saunair/Stepping-Stones/Mechanical/CAD/Model-F/ss_mf_v1_FR_Top_Plate_Assembly.SLDASM

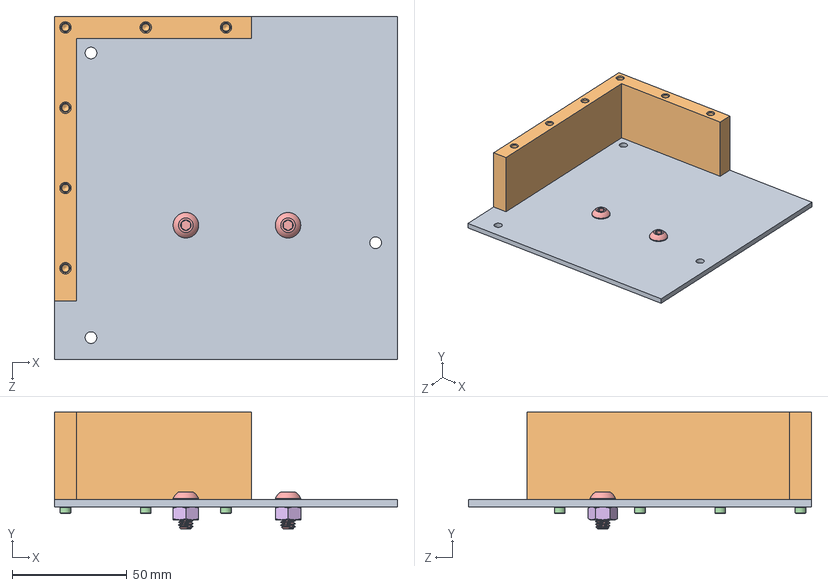
[picture p16: CAD file, 2016-11-26]
Mechanical/CAD/Model-F/ss_mf_v1_FR_Top_Plate_Assembly.SLDASM
149.2 x 50.8 x 149.2 mm
ss_mf_v1_TopPlate
ss_mf_v1_GuideRail
ss_mf_v0_ThreadedInsert440 x 6
ss_mf_v0_Screw_4-40x0.375 x 6
ss_mf_v0_Screw_1_4-20x0.5 x 2
ss_mf_v0_HexNut_1_4-20 x 2
