saunair/Stepping-Stones/Mechanical/CAD/Model-F/Drive Train/ss_mf_v1_DriveTrainAssembly.SLDASM

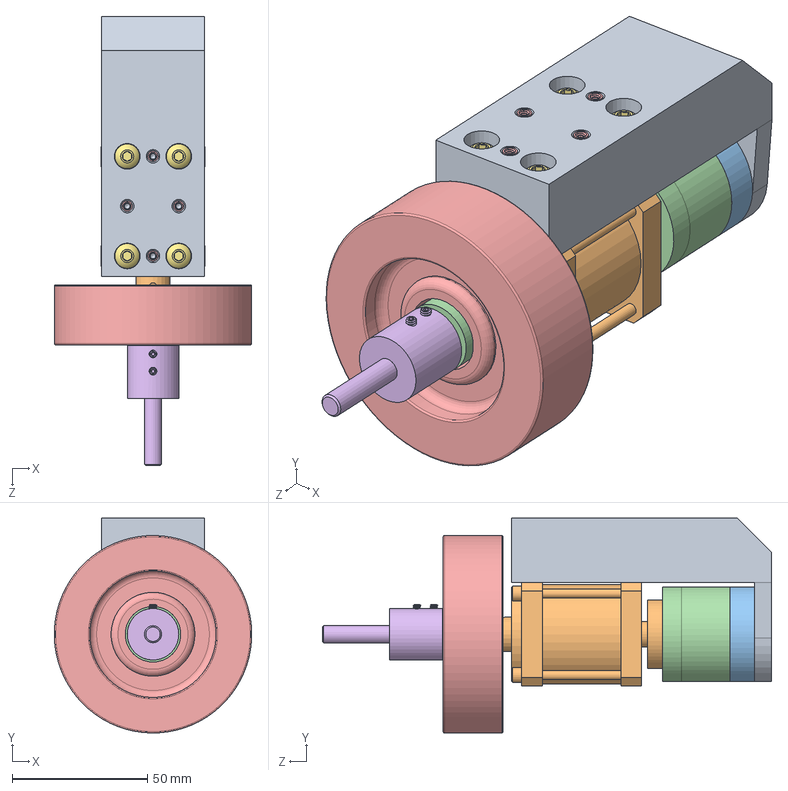
[picture p17: CAD file, 2016-11-26]
Mechanical/CAD/Model-F/Drive Train/ss_mf_v1_DriveTrainAssembly.SLDASM
73.0 x 79.5 x 166.1 mm
ss_mf_v1_GearboxMount
ss_mf_v1_MotorGearboxAdapter
ss_mf_v0_MotorBack
ss_mf_v0_MotorFront
ss_mf_v0_ThreadedInsert440 x 4
ss_mf_v0_SetScrew440 x 2
ss_mf_v0_Screw_10-32x1 x 4
ss_mf_v0_Screw_M3x10 x 4
ss_mf_v0_Screw_M2_5x6 x 3
ss_mf_v0_Gearbox2
ss_mf_v0_Pinion
ss_mf_v0_Hub
ss_mf_v0_Wheel
ss_mf_v1_AuxShaft
