saunair/Stepping-Stones/Mechanical/CAD/Model-F/3D Printing/ss_mf_v2_BearingMount.STL

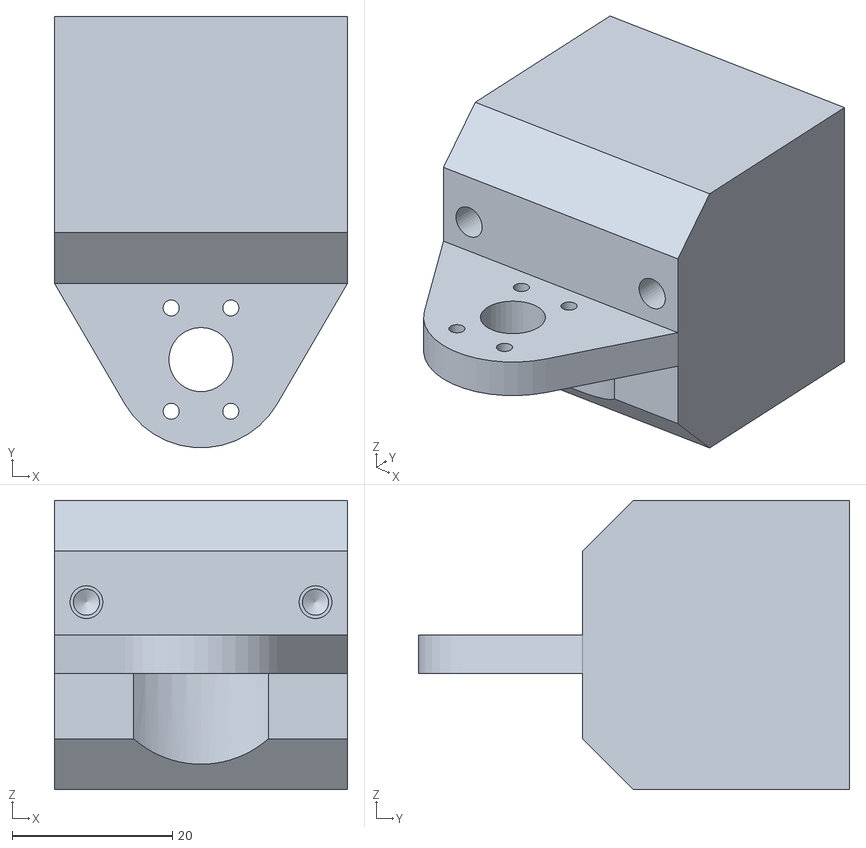
[picture p18: CAD file, 2017-04-23]
Mechanical/CAD/Model-F/3D Printing/ss_mf_v2_BearingMount.STL
36.6 x 53.8 x 36.1
