saunair/Stepping-Stones/Mechanical/CAD/Model-F/Caster Supports/ss_mf_v1_BallCasterMount.SLDPRT

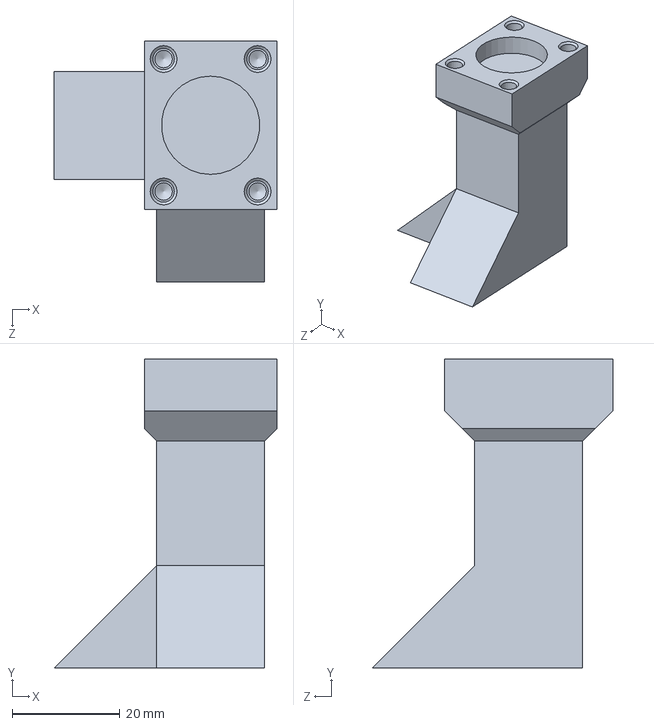
[picture p19: CAD file, 2016-11-26]
Mechanical/CAD/Model-F/Caster Supports/ss_mf_v1_BallCasterMount.SLDPRT
41.4 x 57.4 x 44.7 mm
