saunair/Stepping-Stones/Mechanical/CAD/Model-F/Force Sensing/ss_mf_v1_ForceSensorFoundationSingle.SLDPRT

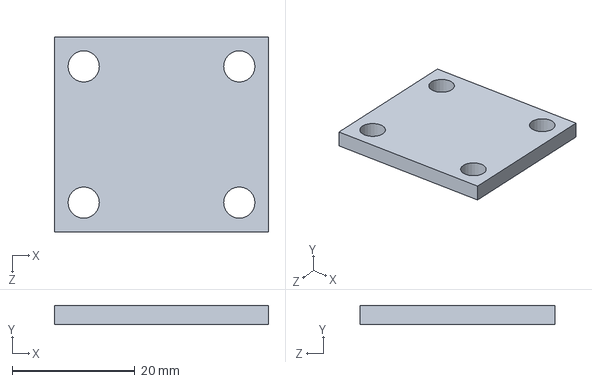
[picture p20: CAD file, 2016-11-26]
Mechanical/CAD/Model-F/Force Sensing/ss_mf_v1_ForceSensorFoundationSingle.SLDPRT
34.9 x 3.17 x 31.8 mm
