saunair/Stepping-Stones/Mechanical/CAD/Model-F/GuideRailFR.SLDPRT

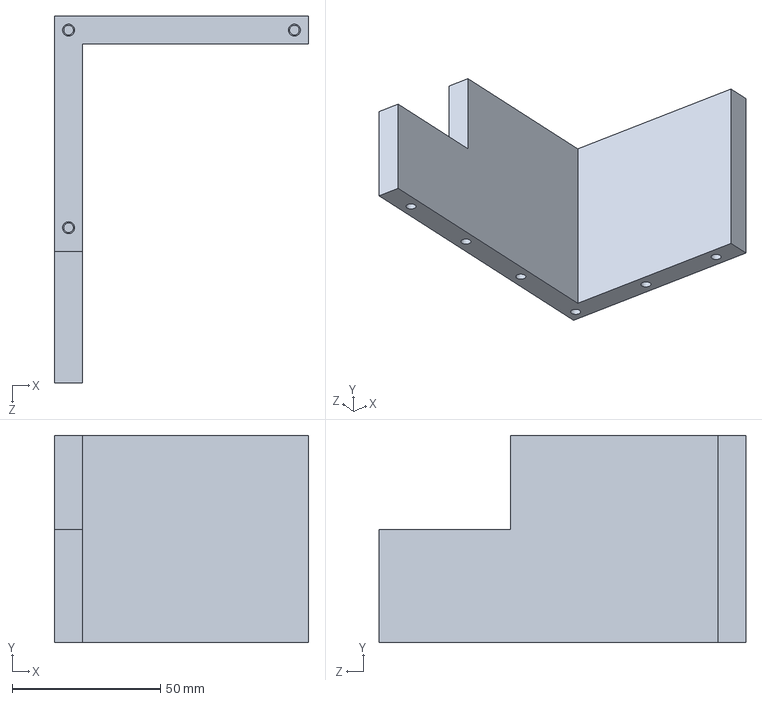
[picture p21: CAD file, 2017-03-23]
Mechanical/CAD/Model-F/GuideRailFR.SLDPRT
85.7 x 69.8 x 123.8 mm
