saunair/Stepping-Stones/Mechanical/CAD/Model-F/PCB/ss_mf_v1_pcbMountP1.SLDPRT

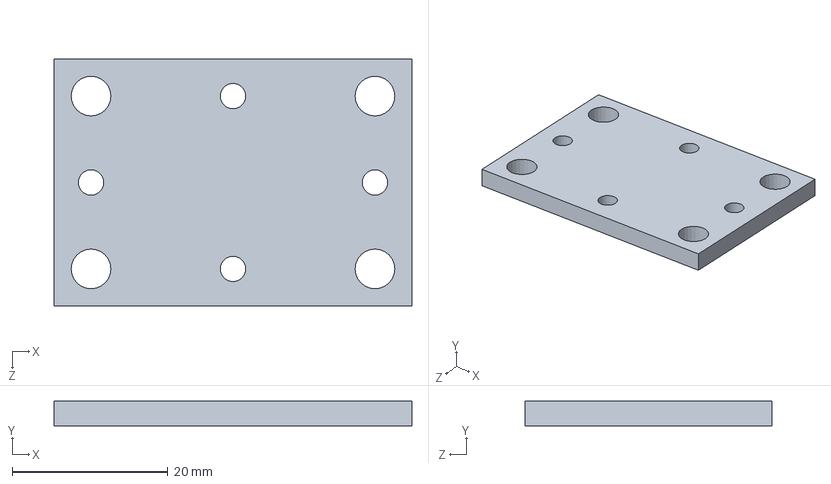
[picture p22: CAD file, 2016-11-26]
Mechanical/CAD/Model-F/PCB/ss_mf_v1_pcbMountP1.SLDPRT
46.0 x 3.17 x 31.8 mm
