saunair/Stepping-Stones/Mechanical/CAD/Model-F/Waterjet Cutting/ss_mf_v1_TopPlateBack.DXF

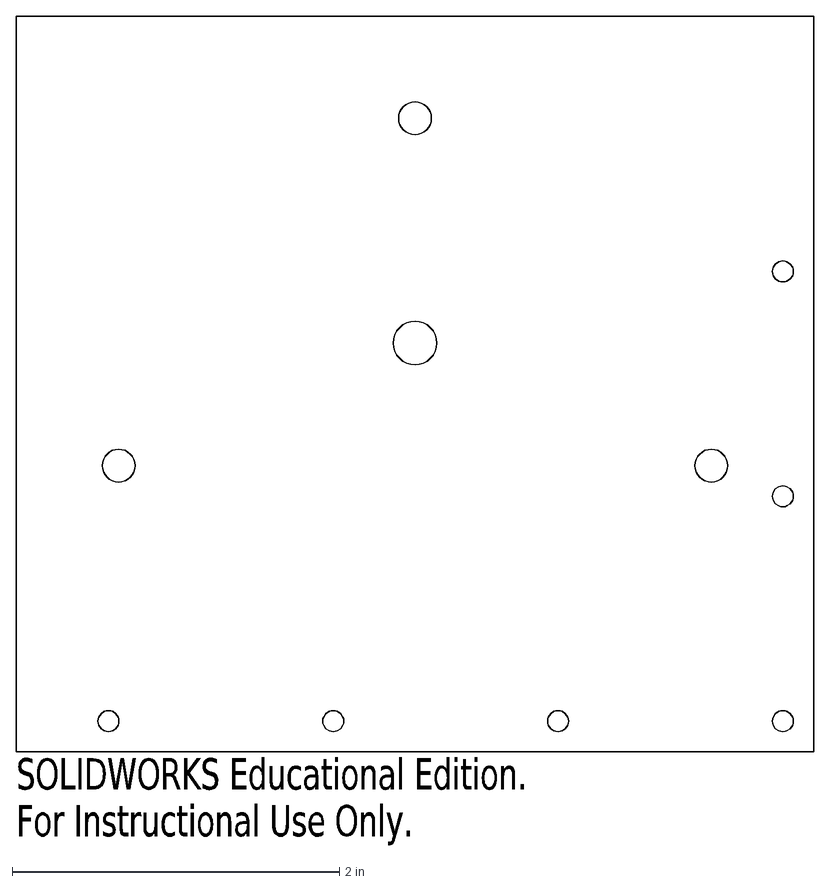
[picture p23: CAD file, 2016-11-26]
Mechanical/CAD/Model-F/Waterjet Cutting/ss_mf_v1_TopPlateBack.DXF
SOLIDWORKS Educational Edition.
For Instructional Use Only.
