saunair/Stepping-Stones/Mechanical/CAD/Model-F/3D Printing/ss_mf_v1_ForceSensorLocatorSingle.STL

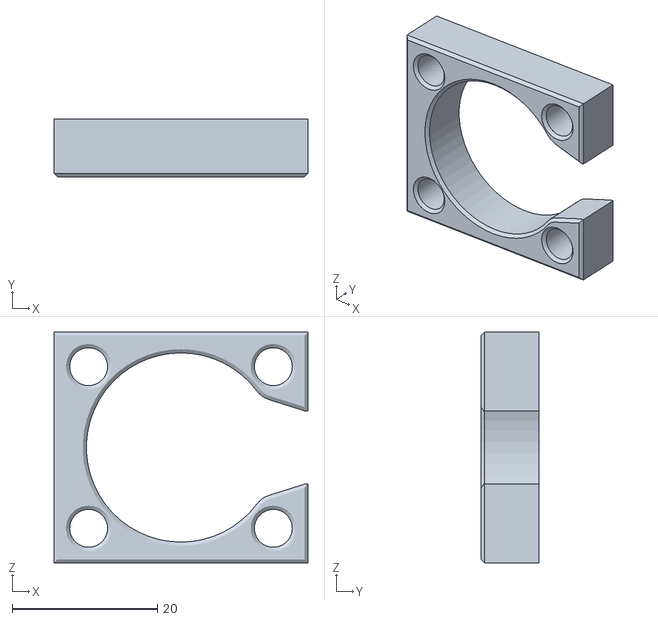
[picture p24: CAD file, 2016-11-26]
Mechanical/CAD/Model-F/3D Printing/ss_mf_v1_ForceSensorLocatorSingle.STL
34.9 x 8.00 x 31.8
