saunair/Stepping-Stones/Mechanical/CAD/Model-F/ArduinoMountRight.SLDPRT

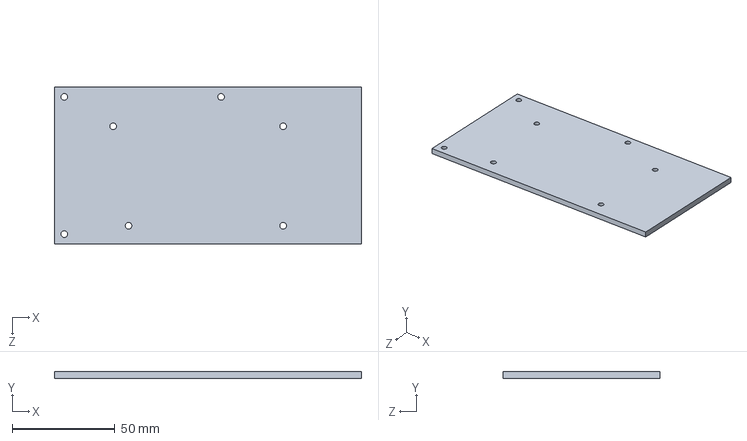
[picture p25: CAD file, 2017-03-23]
Mechanical/CAD/Model-F/ArduinoMountRight.SLDPRT
149.2 x 3.17 x 76.2 mm
