saunair/Stepping-Stones/Mechanical/CAD/Model-F/Force Sensing/ss_mf_v1_ForceSensorFoundation.SLDPRT

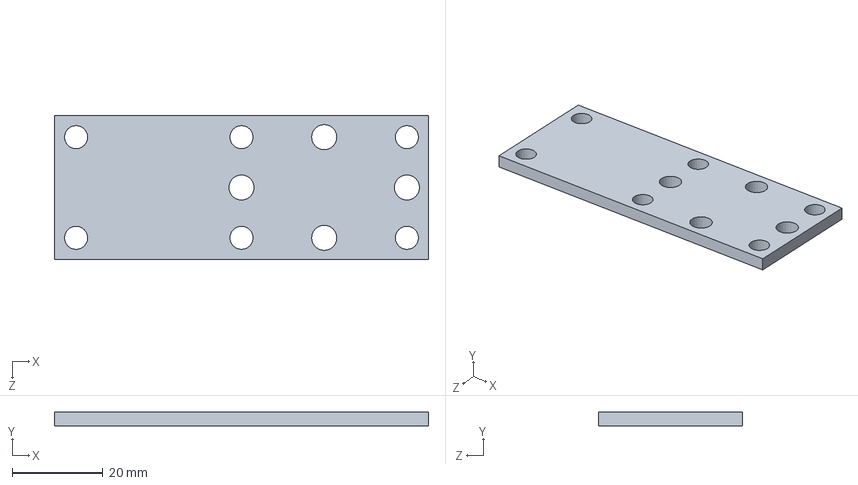
[picture p26: CAD file, 2016-11-26]
Mechanical/CAD/Model-F/Force Sensing/ss_mf_v1_ForceSensorFoundation.SLDPRT
82.5 x 3.17 x 31.8 mm
