saunair/Stepping-Stones/Mechanical/CAD/Model-S/ss_ms_v1_SkateWheelMount_RearInner.SLDPRT

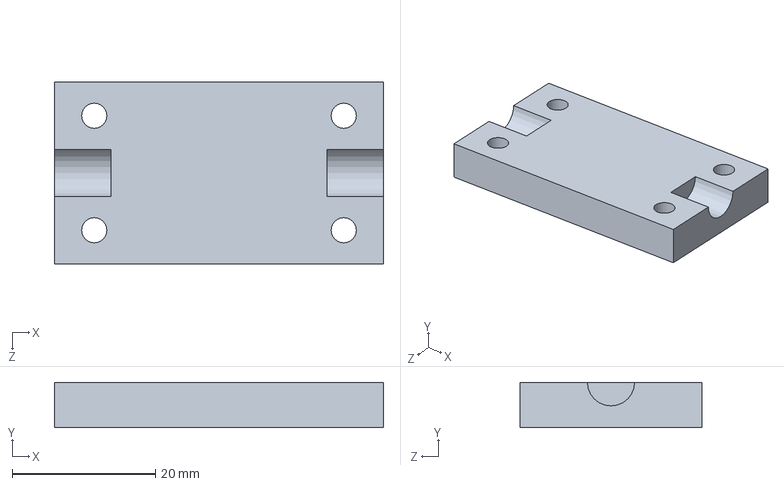
[picture p28: CAD file, 2017-04-23]
Mechanical/CAD/Model-S/ss_ms_v1_SkateWheelMount_RearInner.SLDPRT
46.0 x 6.35 x 25.4 mm
