saunair/Stepping-Stones/Mechanical/CAD/Model-F/3D Printing/ss_mf_v1_GearboxMount-3DPrint.SLDPRT

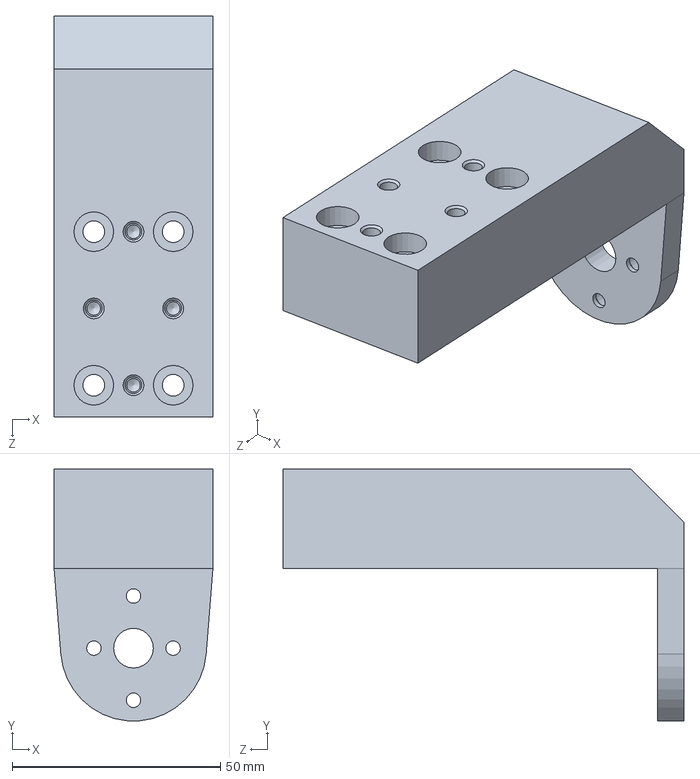
[picture p29: CAD file, 2016-11-26]
Mechanical/CAD/Model-F/3D Printing/ss_mf_v1_GearboxMount-3DPrint.SLDPRT
38.1 x 60.4 x 96.2 mm
