saunair/Stepping-Stones/Mechanical/CAD/Model-F/Caster Supports/ss_mf_v0_BallCaster.SLDPRT

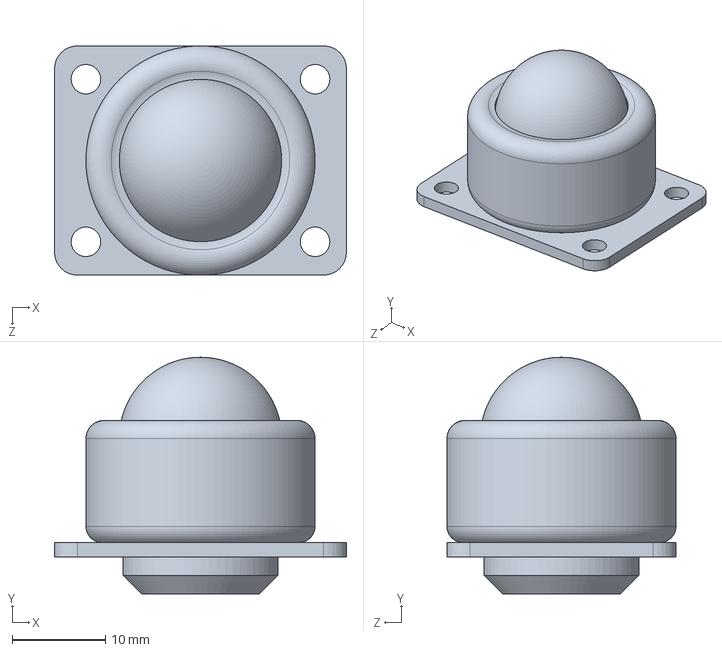
[picture p30: CAD file, 2016-11-26]
Mechanical/CAD/Model-F/Caster Supports/ss_mf_v0_BallCaster.SLDPRT
31.4 x 25.4 x 24.6 mm
