saunair/Stepping-Stones/Mechanical/CAD/Model-F/Drive Train/ss_mf_v0_MotorBack.SLDPRT

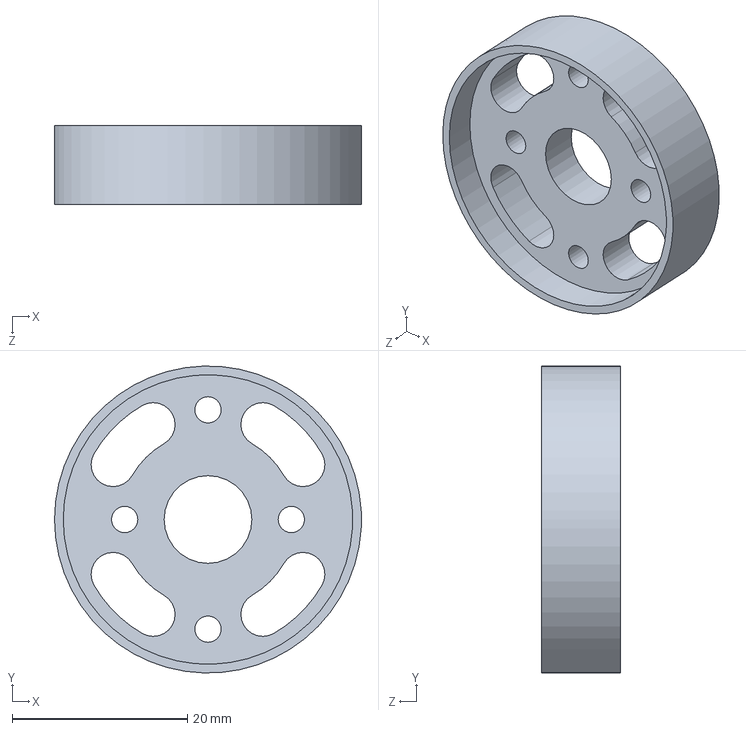
[picture p31: CAD file, 2016-11-26]
Mechanical/CAD/Model-F/Drive Train/ss_mf_v0_MotorBack.SLDPRT
35.0 x 35.0 x 9.00 mm
