saunair/Stepping-Stones/Mechanical/CAD/Model-F/Hardware/ss_mf_v0_Standoff_4-40x0.5.SLDPRT

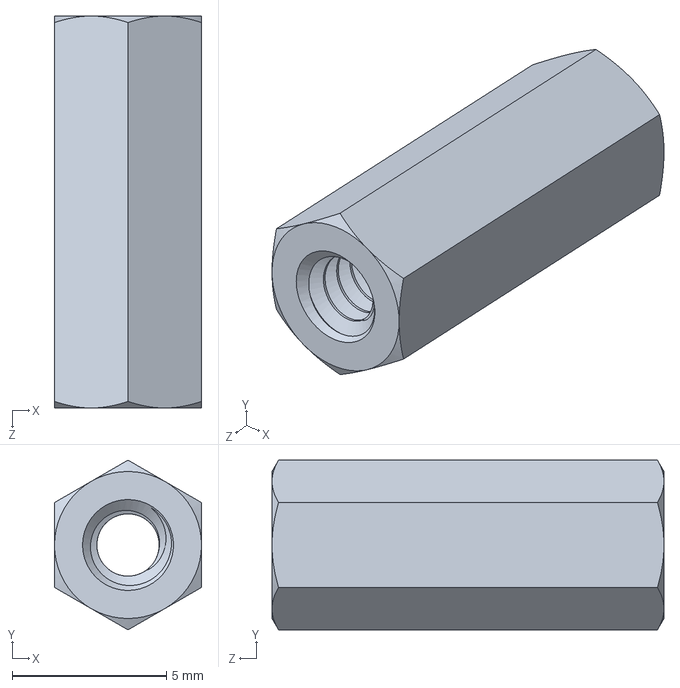
[picture p32: CAD file, 2016-11-26]
Mechanical/CAD/Model-F/Hardware/ss_mf_v0_Standoff_4-40x0.5.SLDPRT
4.76 x 5.50 x 12.7 mm
