saunair/Stepping-Stones/Mechanical/CAD/Model-F/Waterjet Cutting/ss_mf_v1_BasePlate.DXF

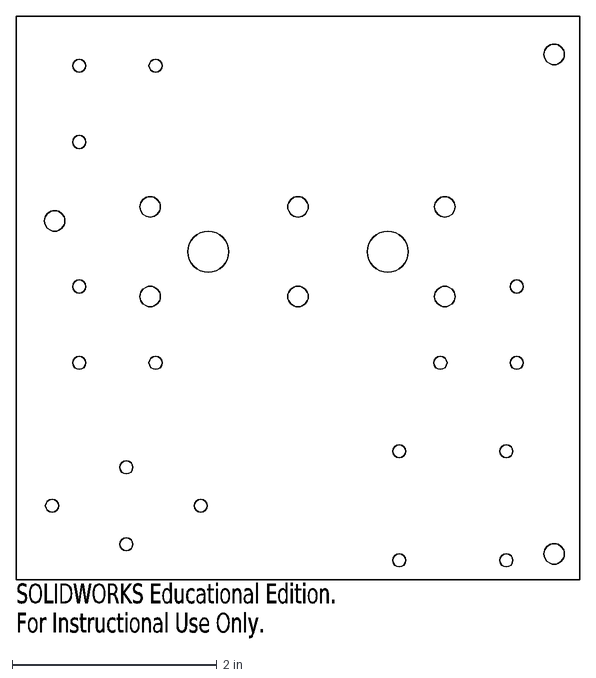
[picture p33: CAD file, 2016-11-26]
Mechanical/CAD/Model-F/Waterjet Cutting/ss_mf_v1_BasePlate.DXF
SOLIDWORKS Educational Edition.
For Instructional Use Only.
