saunair/Stepping-Stones/Mechanical/CAD/Model-F/3D Printing/ss_mf_v1_imuMount-3DPrint.SLDPRT

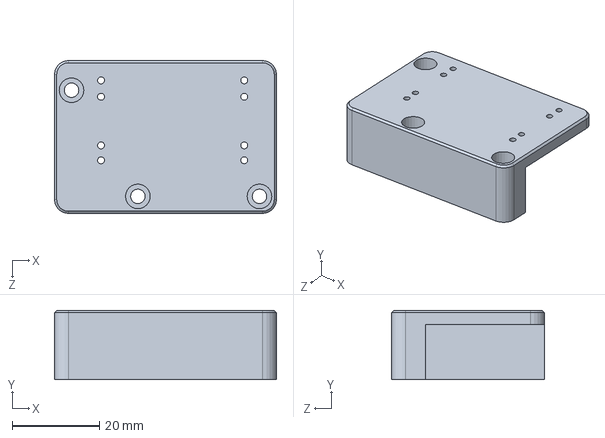
[picture p34: CAD file, 2016-11-26]
Mechanical/CAD/Model-F/3D Printing/ss_mf_v1_imuMount-3DPrint.SLDPRT
51.0 x 15.9 x 35.1 mm
