saunair/Stepping-Stones/Mechanical/CAD/Model-F/Drive Train/ss_mf_v0_Wheel.SLDPRT

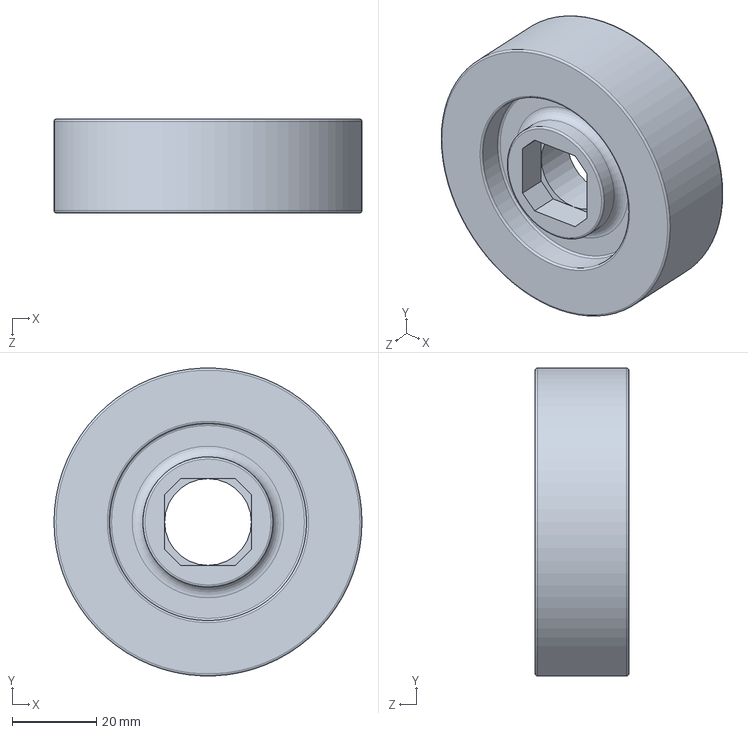
[picture p35: CAD file, 2016-11-26]
Mechanical/CAD/Model-F/Drive Train/ss_mf_v0_Wheel.SLDPRT
73.0 x 73.0 x 22.2 mm
