saunair/Stepping-Stones/Mechanical/CAD/Model-F/Waterjet Cutting/ss_mf_v1_BasePlateBack.DXF

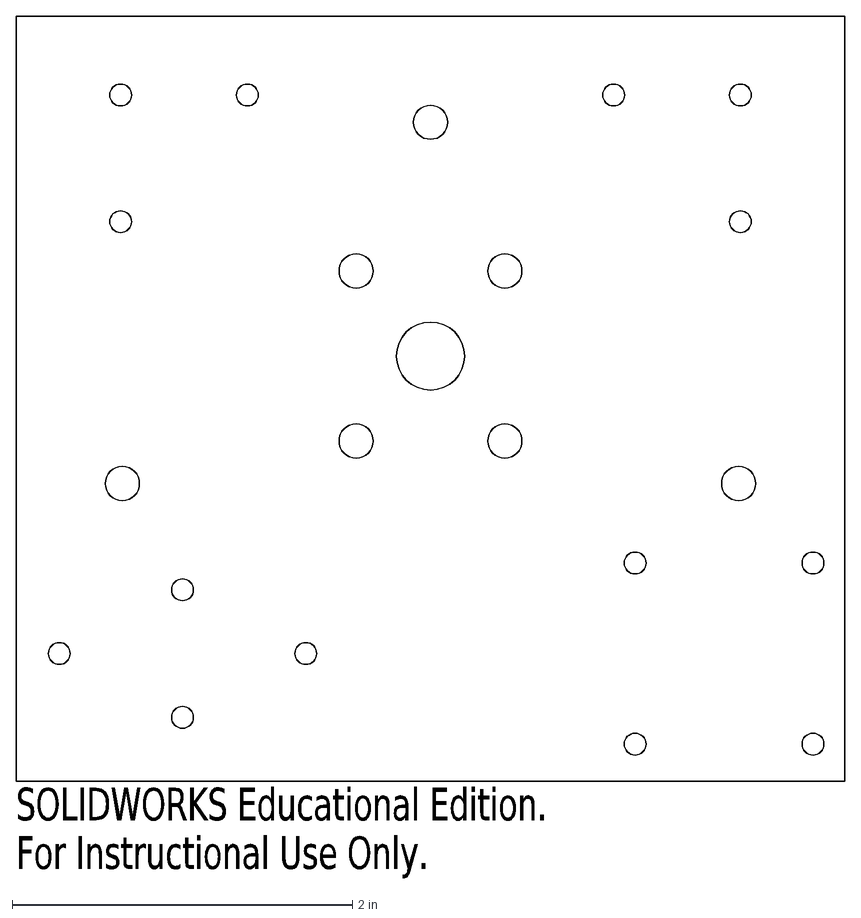
[picture p36: CAD file, 2016-11-26]
Mechanical/CAD/Model-F/Waterjet Cutting/ss_mf_v1_BasePlateBack.DXF
SOLIDWORKS Educational Edition.
For Instructional Use Only.
