saunair/Stepping-Stones/Mechanical/CAD/Model-S/ss_ms_v0_SkateWheel.SLDPRT

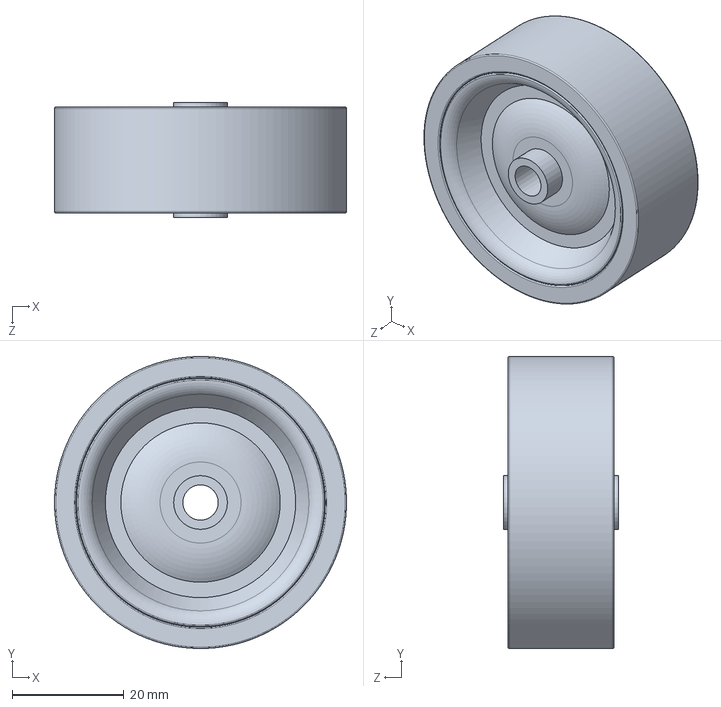
[picture p37: CAD file, 2017-04-23]
Mechanical/CAD/Model-S/ss_ms_v0_SkateWheel.SLDPRT
52.4 x 52.4 x 20.6 mm
