saunair/Stepping-Stones/Mechanical/CAD/Model-F/Drive Train/ss_mf_v1_AuxShaft.SLDPRT

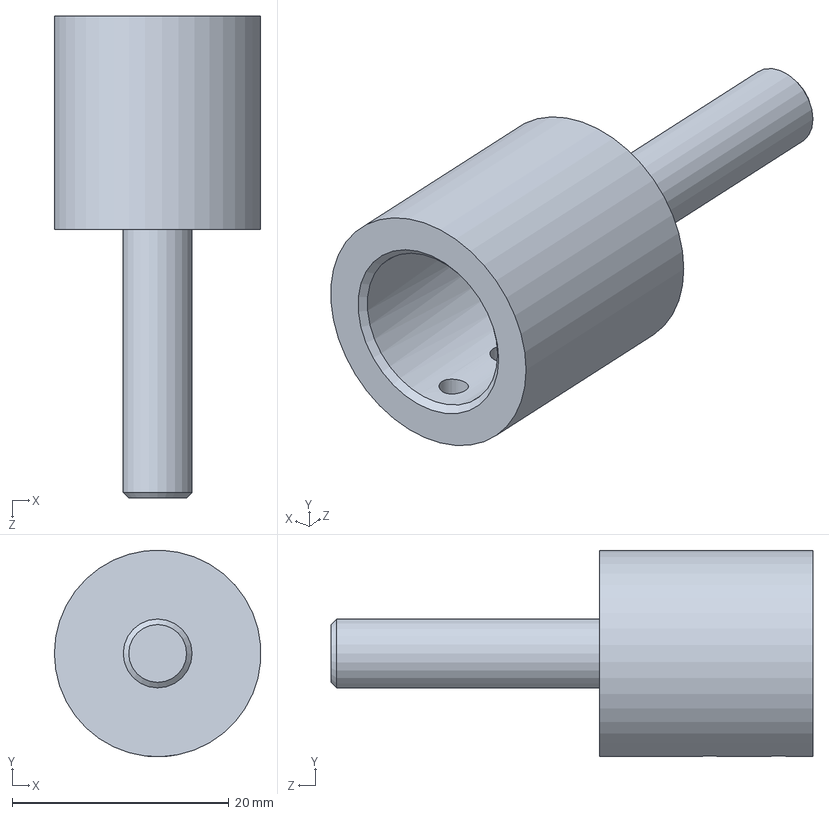
[picture p38: CAD file, 2016-11-26]
Mechanical/CAD/Model-F/Drive Train/ss_mf_v1_AuxShaft.SLDPRT
19.0 x 19.0 x 44.5 mm
