saunair/Stepping-Stones/Mechanical/CAD/Model-F/Force Sensing/ss_mf_v1_ForceSensorLocatorSingle.SLDPRT

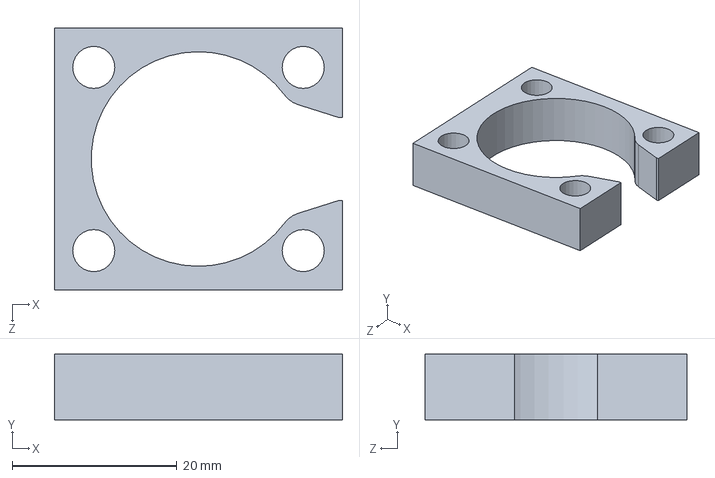
[picture p39: CAD file, 2016-11-26]
Mechanical/CAD/Model-F/Force Sensing/ss_mf_v1_ForceSensorLocatorSingle.SLDPRT
34.9 x 8.00 x 31.8 mm
