saunair/Stepping-Stones/Mechanical/CAD/Model-F/Waterjet Cutting/ss_mf_v1_ForceSensorFoundationDual.DXF

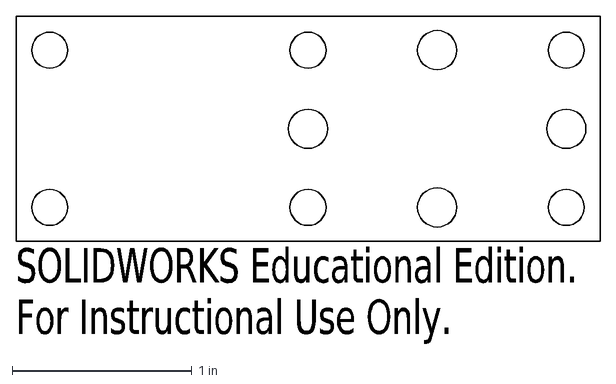
[picture p40: CAD file, 2016-11-26]
Mechanical/CAD/Model-F/Waterjet Cutting/ss_mf_v1_ForceSensorFoundationDual.DXF
SOLIDWORKS Educational Edition.
For Instructional Use Only.
