saunair/Stepping-Stones/Mechanical/CAD/Model-S/ss_ms_v0_DowelPinShaft.SLDPRT

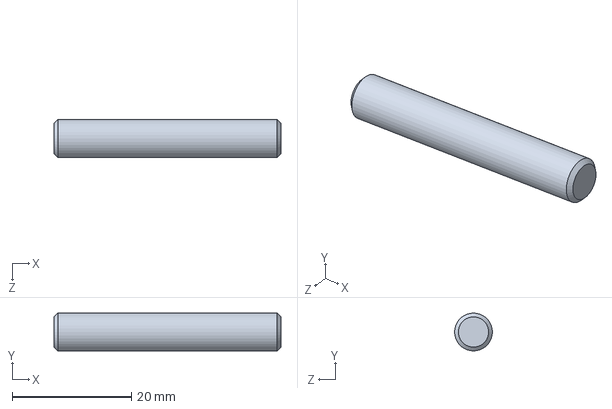
[picture p41: CAD file, 2017-04-23]
Mechanical/CAD/Model-S/ss_ms_v0_DowelPinShaft.SLDPRT
38.1 x 6.35 x 6.35 mm
