saunair/Stepping-Stones/Mechanical/CAD/Model-F/Drive Train/ss_mf_v0_Wheel_Hub.SLDPRT

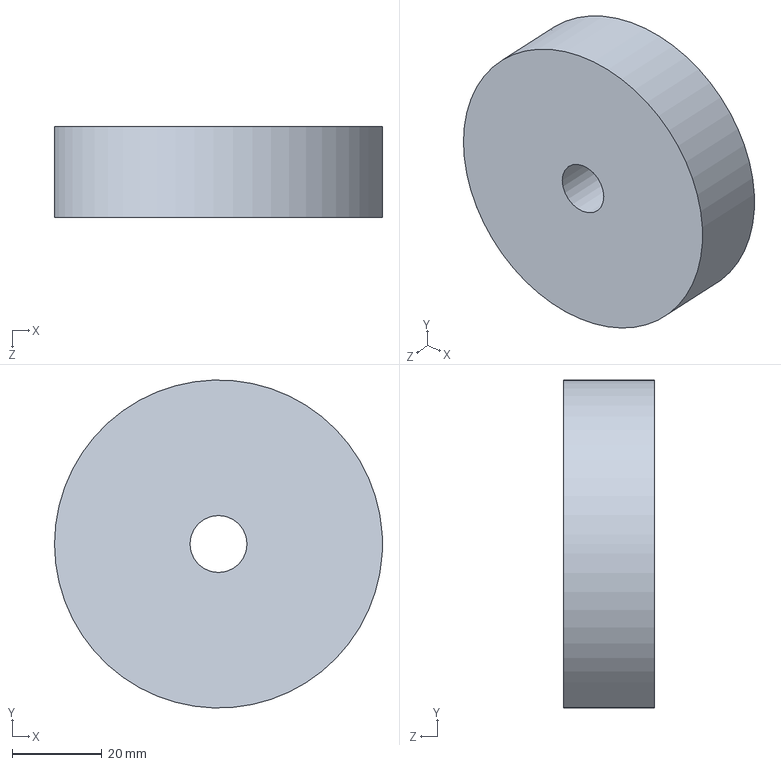
[picture p42: CAD file, 2016-11-26]
Mechanical/CAD/Model-F/Drive Train/ss_mf_v0_Wheel_Hub.SLDPRT
73.0 x 73.0 x 20.3 mm
