saunair/Stepping-Stones/Mechanical/CAD/Model-F/Force Sensing/ss_mf_v1_ForceSensorLocatorDual.SLDPRT

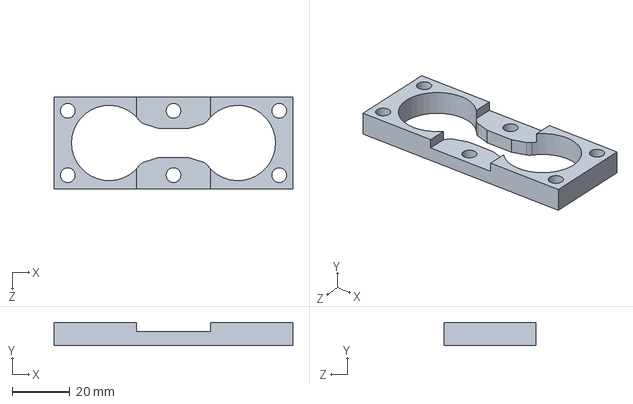
[picture p43: CAD file, 2016-11-26]
Mechanical/CAD/Model-F/Force Sensing/ss_mf_v1_ForceSensorLocatorDual.SLDPRT
82.5 x 8.00 x 31.8 mm
