saunair/Stepping-Stones/Mechanical/CAD/Model-F/Hardware/ss_mf_v0_HexNut_1_4-20.SLDPRT

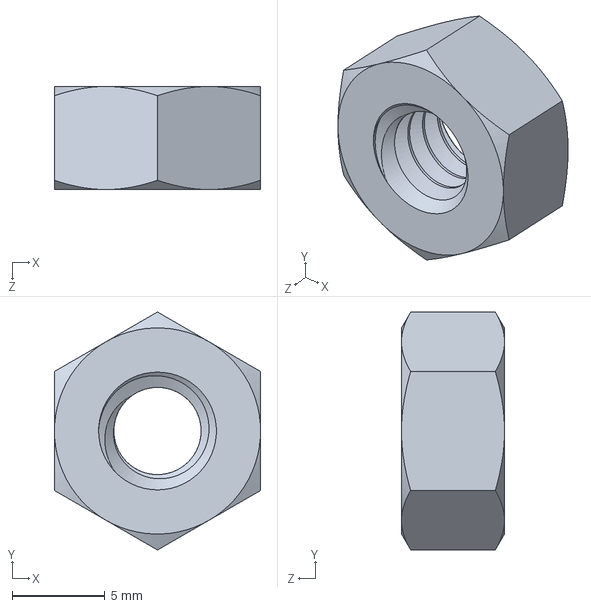
[picture p44: CAD file, 2016-11-26]
Mechanical/CAD/Model-F/Hardware/ss_mf_v0_HexNut_1_4-20.SLDPRT
11.1 x 12.8 x 5.56 mm
