saunair/Stepping-Stones/Mechanical/CAD/Model-F/PCB/UWS.SLDPRT

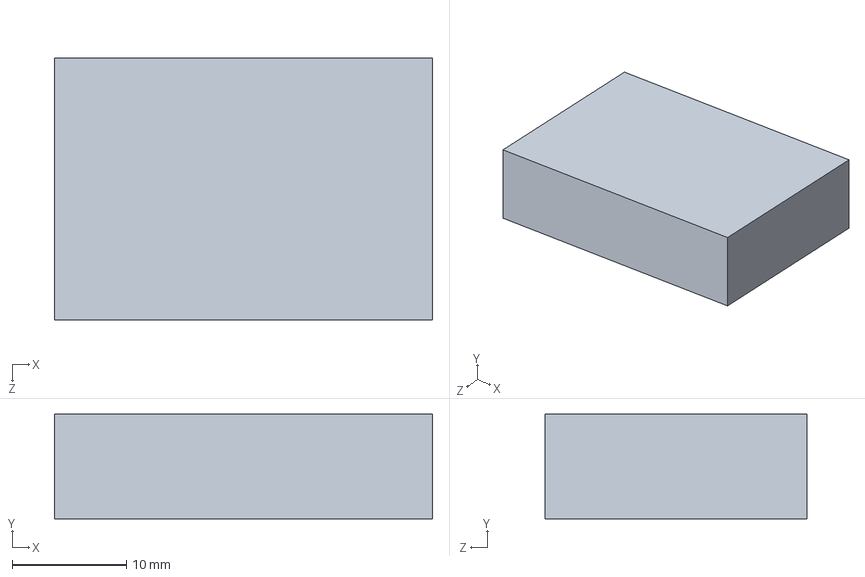
[picture p45: CAD file, 2016-11-26]
Mechanical/CAD/Model-F/PCB/UWS.SLDPRT
33.0 x 9.14 x 22.9 mm
