saunair/Stepping-Stones/Mechanical/CAD/Model-F/Waterjet Cutting/ss_mf_v1_ForceSensorFoundationSingle.DXF

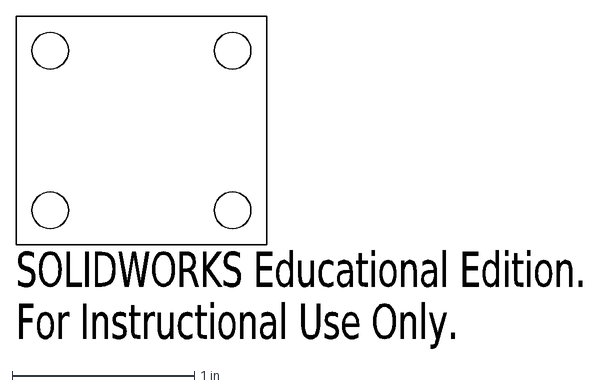
[picture p46: CAD file, 2016-11-26]
Mechanical/CAD/Model-F/Waterjet Cutting/ss_mf_v1_ForceSensorFoundationSingle.DXF
SOLIDWORKS Educational Edition.
For Instructional Use Only.
