saunair/Stepping-Stones/Mechanical/CAD/Model-S/ss_ms_v1_SkateWheelMount_FrontInner.SLDPRT

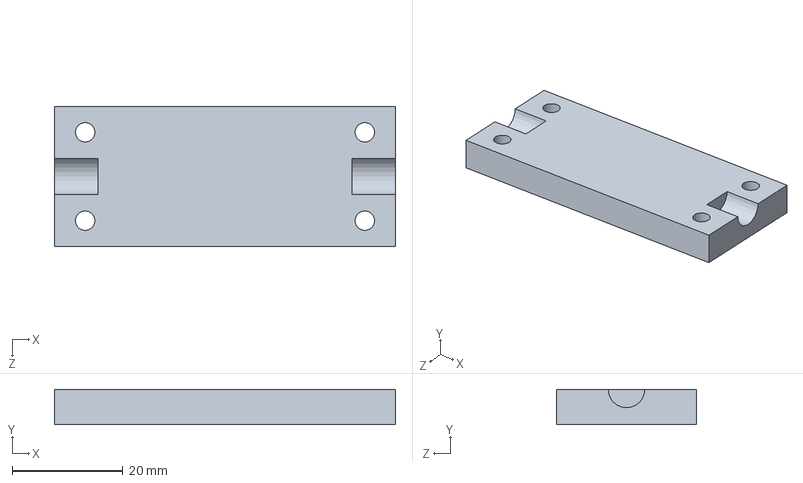
[picture p47: CAD file, 2017-04-23]
Mechanical/CAD/Model-S/ss_ms_v1_SkateWheelMount_FrontInner.SLDPRT
61.7 x 6.35 x 25.4 mm
