saunair/Stepping-Stones/Mechanical/CAD/Model-F/Force Sensing/ss_mf_v0_ForceSensor.SLDPRT

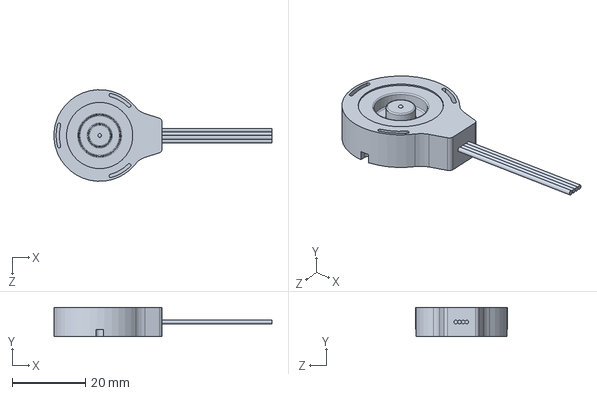
[picture p48: CAD file, 2016-11-26]
Mechanical/CAD/Model-F/Force Sensing/ss_mf_v0_ForceSensor.SLDPRT
59.5 x 8.00 x 25.0 mm
