saunair/Stepping-Stones/Mechanical/CAD/Model-F/Hardware/ss_mf_v0_HexNut_10-32.SLDPRT

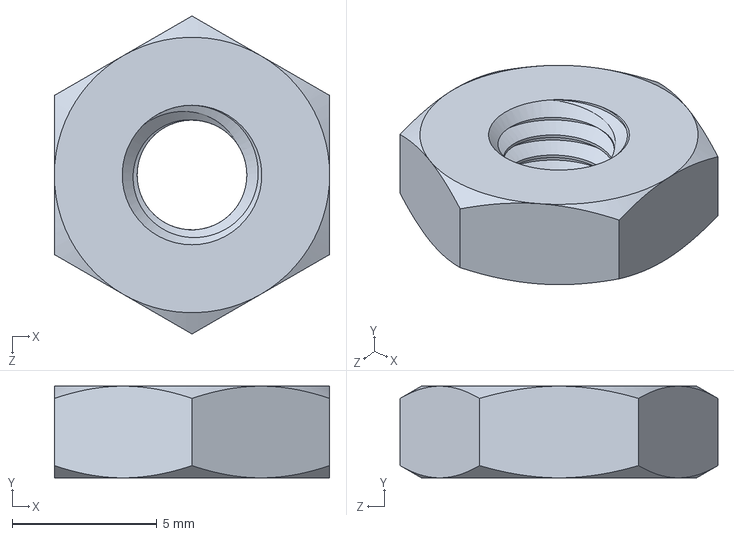
[picture p49: CAD file, 2016-11-26]
Mechanical/CAD/Model-F/Hardware/ss_mf_v0_HexNut_10-32.SLDPRT
9.53 x 3.17 x 11.0 mm
