saunair/Stepping-Stones/Mechanical/CAD/Model-S/ss_ms_v1_SkateWheelFork.SLDPRT

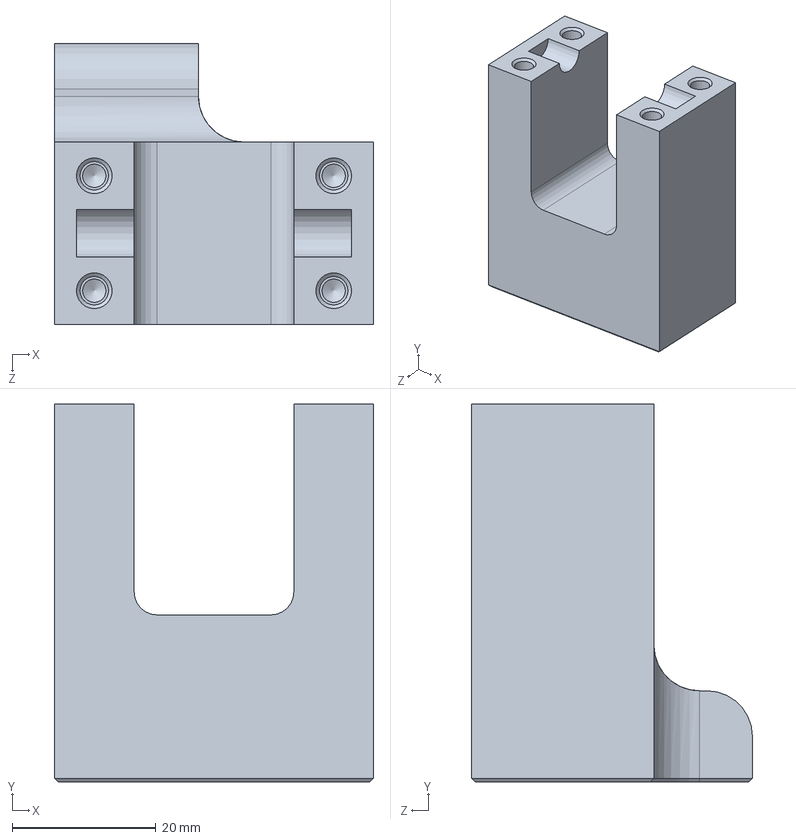
[picture p50: CAD file, 2017-04-23]
Mechanical/CAD/Model-S/ss_ms_v1_SkateWheelFork.SLDPRT
44.5 x 52.6 x 39.1 mm
