saunair/Stepping-Stones/Mechanical/CAD/Model-F/Drive Train/ss_mf_v1_MotorGearboxAdapter.SLDPRT

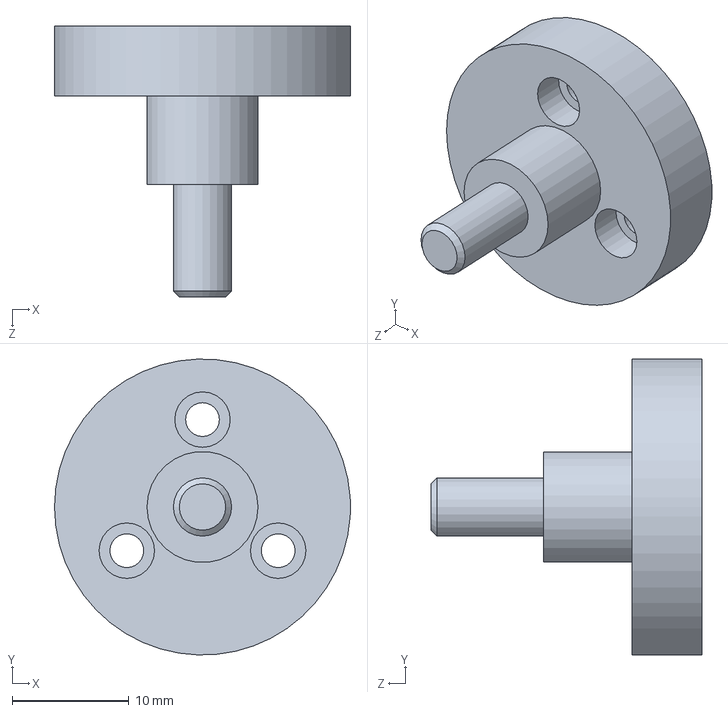
[picture p51: CAD file, 2016-11-26]
Mechanical/CAD/Model-F/Drive Train/ss_mf_v1_MotorGearboxAdapter.SLDPRT
25.4 x 25.4 x 23.3 mm
