saunair/Stepping-Stones/Mechanical/CAD/Model-F/Hardware/ss_mf_v0_ThreadedInsert440.SLDPRT

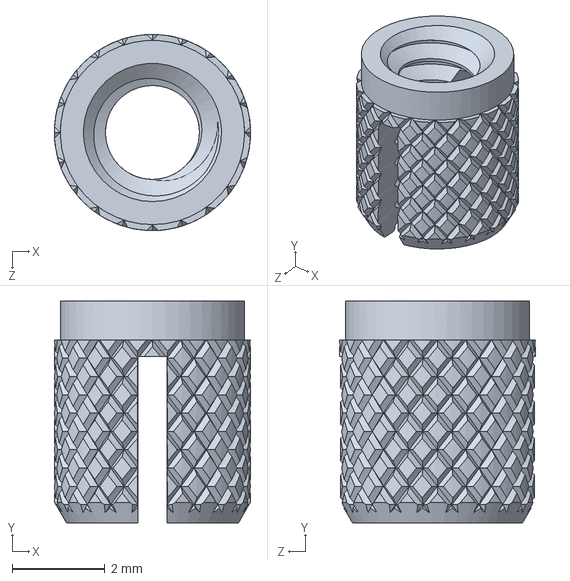
[picture p52: CAD file, 2016-11-26]
Mechanical/CAD/Model-F/Hardware/ss_mf_v0_ThreadedInsert440.SLDPRT
4.22 x 4.78 x 4.22 mm
