saunair/Stepping-Stones/Mechanical/CAD/Model-F/ss_mf_v1_GuideRail.SLDPRT

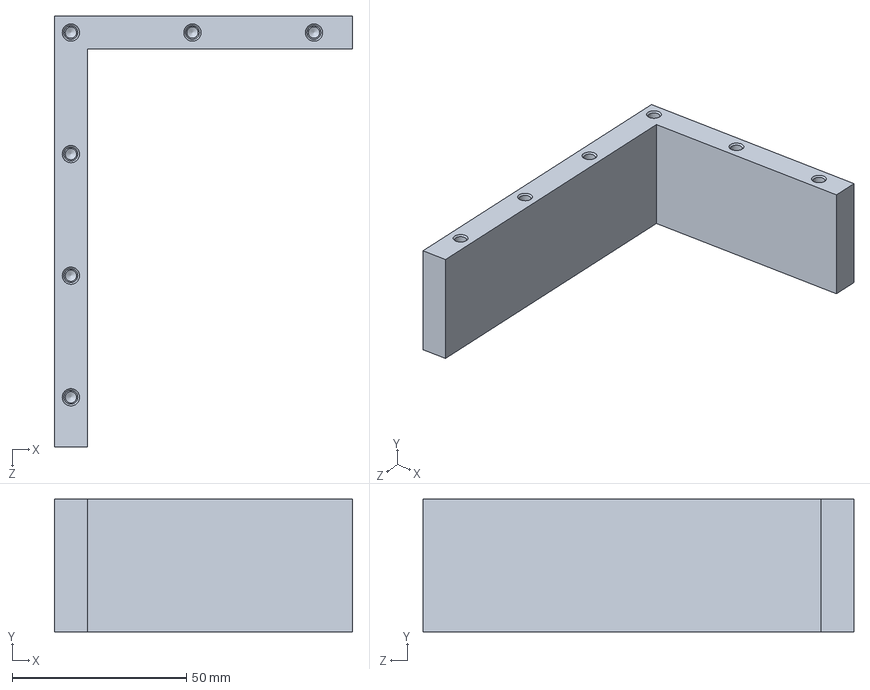
[picture p53: CAD file, 2016-11-26]
Mechanical/CAD/Model-F/ss_mf_v1_GuideRail.SLDPRT
85.7 x 38.1 x 123.8 mm
