saunair/Stepping-Stones/Mechanical/CAD/Model-S/ss_ms_v1_SkateWheelMount_Outer.SLDPRT

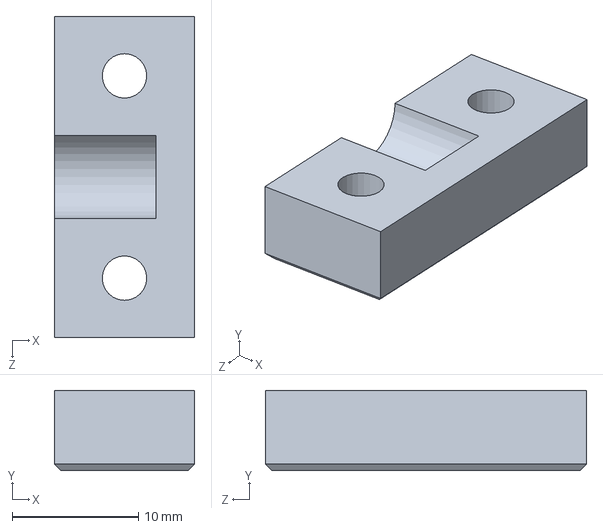
[picture p54: CAD file, 2017-04-23]
Mechanical/CAD/Model-S/ss_ms_v1_SkateWheelMount_Outer.SLDPRT
11.1 x 6.35 x 25.4 mm
