saunair/Stepping-Stones/Mechanical/CAD/Force Calibration Rig/Front Skate Rig Block.SLDPRT

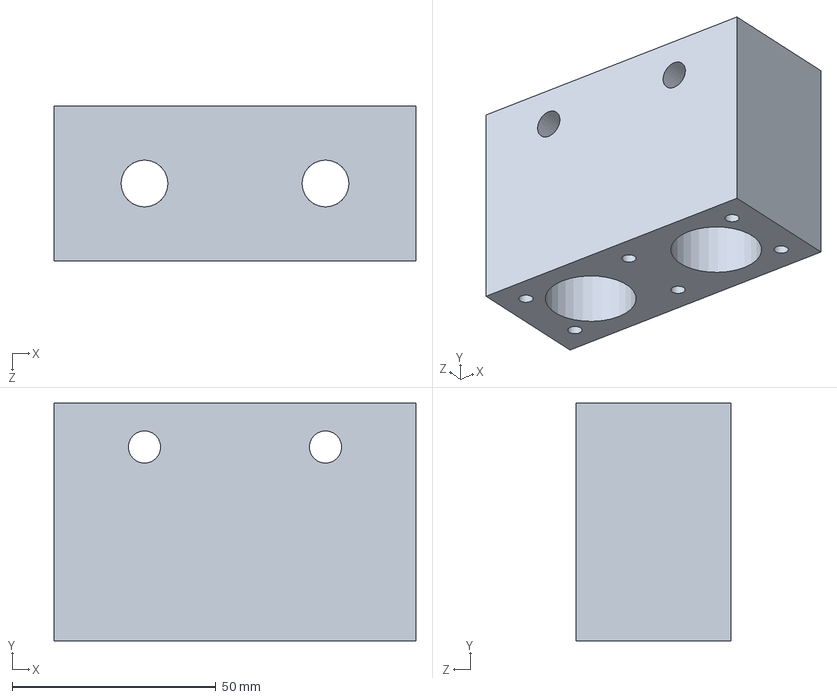
[picture p55: CAD file, 2017-03-11]
Mechanical/CAD/Force Calibration Rig/Front Skate Rig Block.SLDPRT
88.9 x 58.4 x 38.1 mm
