saunair/Stepping-Stones/Mechanical/CAD/Model-F/3D Printing/ss_mf_v1_AuxShaft-3DPrint.SLDPRT

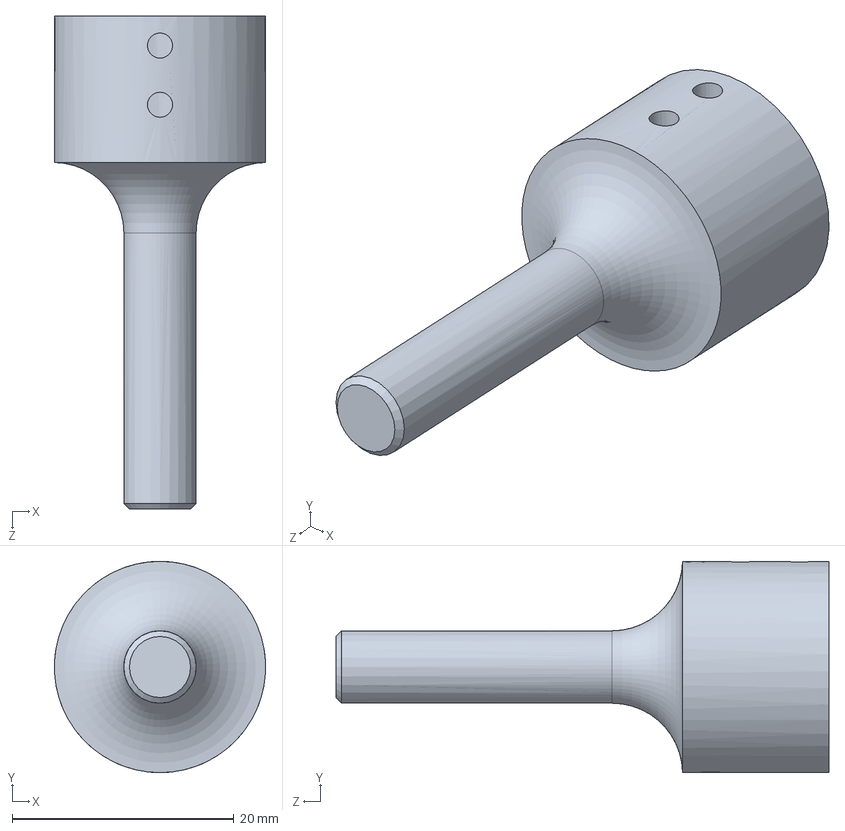
[picture p56: CAD file, 2016-11-26]
Mechanical/CAD/Model-F/3D Printing/ss_mf_v1_AuxShaft-3DPrint.SLDPRT
19.0 x 19.0 x 44.5 mm
