saunair/Stepping-Stones/Mechanical/CAD/Model-F/ss_mf_v1_ESC.SLDPRT

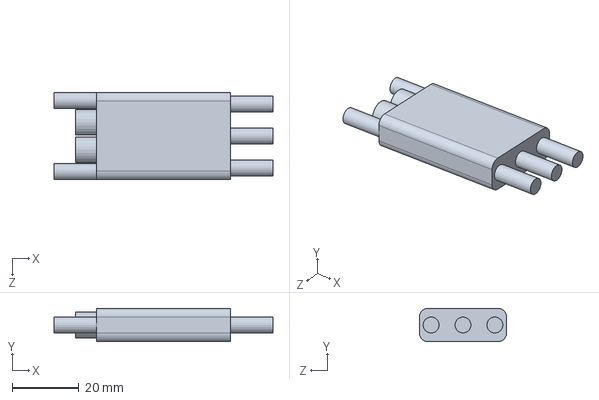
[picture p57: CAD file, 2016-11-26]
Mechanical/CAD/Model-F/ss_mf_v1_ESC.SLDPRT
65.4 x 10.0 x 26.0 mm
