saunair/Stepping-Stones/Mechanical/CAD/Model-F/Drive Train/ss_mf_v0_Hub.SLDPRT

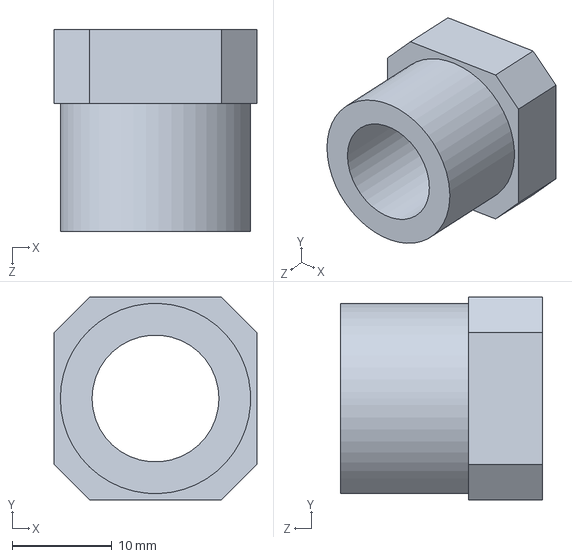
[picture p58: CAD file, 2016-11-26]
Mechanical/CAD/Model-F/Drive Train/ss_mf_v0_Hub.SLDPRT
20.3 x 20.3 x 20.3 mm
