saunair/Stepping-Stones/Mechanical/CAD/Model-F/ss_mf_v1_TopPlate.SLDPRT

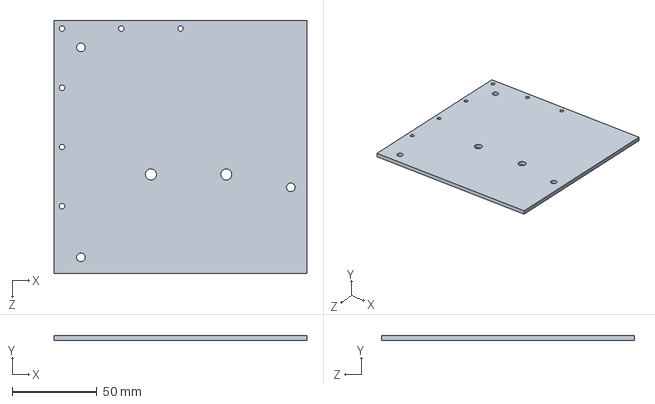
[picture p59: CAD file, 2016-11-26]
Mechanical/CAD/Model-F/ss_mf_v1_TopPlate.SLDPRT
149.2 x 3.17 x 149.2 mm
