saunair/Stepping-Stones/Mechanical/CAD/Model-S/ss_ms_v1_spadeterminals.SLDPRT

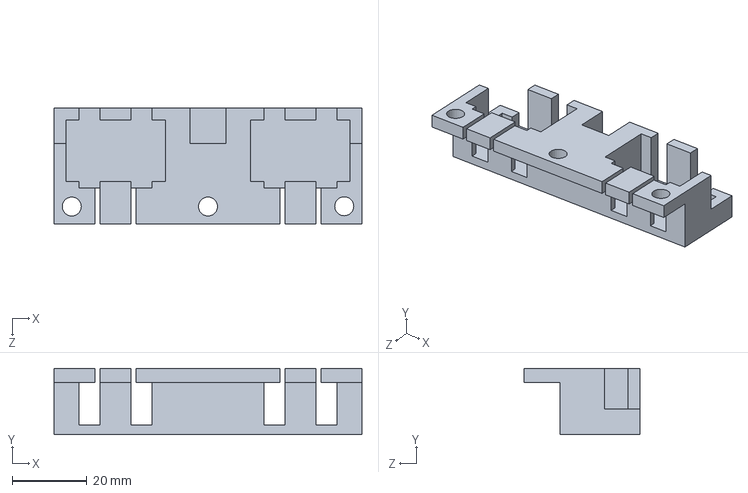
[picture p60: CAD file, 2017-03-16]
Mechanical/CAD/Model-S/ss_ms_v1_spadeterminals.SLDPRT
82.5 x 17.8 x 31.1 mm
