saunair/Stepping-Stones/Mechanical/CAD/Model-F/3D Printing/ss_mf_v1_pcbMountP2.STL

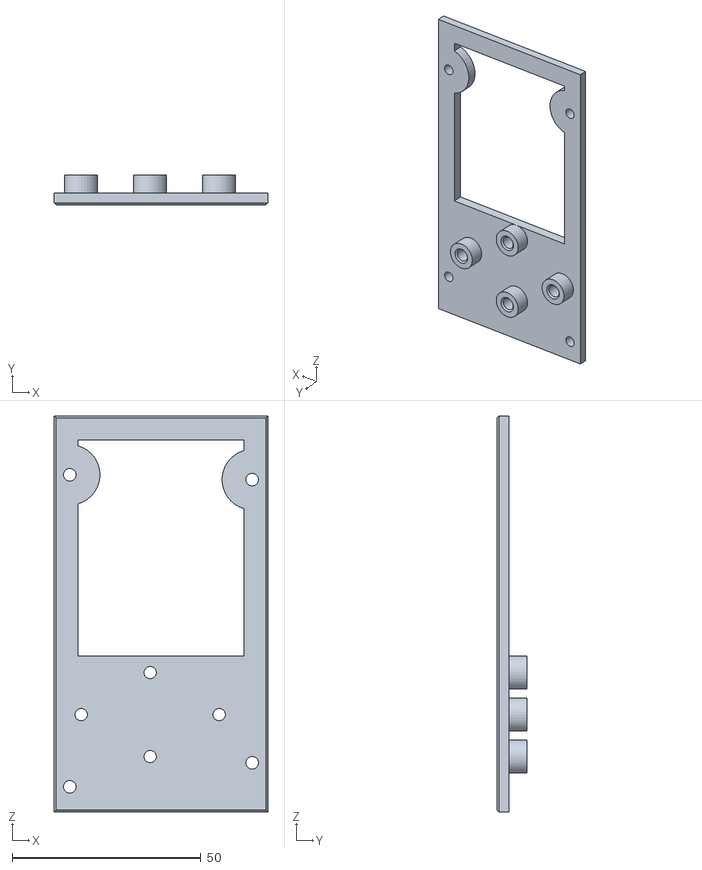
[picture p61: CAD file, 2016-11-26]
Mechanical/CAD/Model-F/3D Printing/ss_mf_v1_pcbMountP2.STL
56.5 x 7.94 x 104.8
