saunair/Stepping-Stones/Mechanical/CAD/Model-S/ss_ms_v1_rear_terminal_holder.SLDPRT

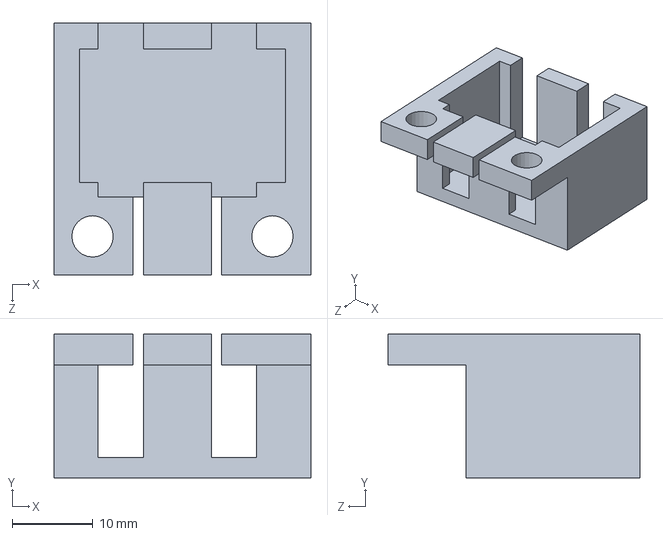
[picture p62: CAD file, 2017-03-16]
Mechanical/CAD/Model-S/ss_ms_v1_rear_terminal_holder.SLDPRT
31.8 x 17.8 x 31.1 mm
