saunair/Stepping-Stones/Mechanical/CAD/Model-F/3D Printing/ss_mf_v1_MotorGearboxAdapter-3DPrint.SLDPRT

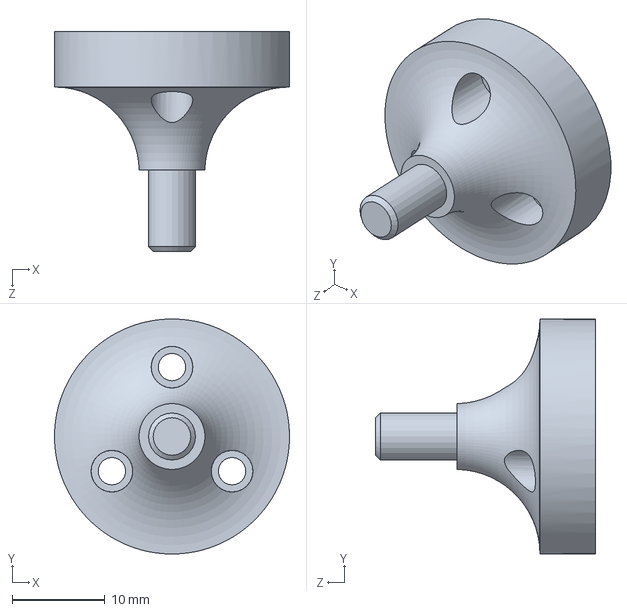
[picture p63: CAD file, 2016-11-26]
Mechanical/CAD/Model-F/3D Printing/ss_mf_v1_MotorGearboxAdapter-3DPrint.SLDPRT
25.4 x 25.4 x 23.8 mm
