saunair/Stepping-Stones/Mechanical/CAD/Model-F/Drive Train/ss_mf_v0_Pinion.SLDPRT

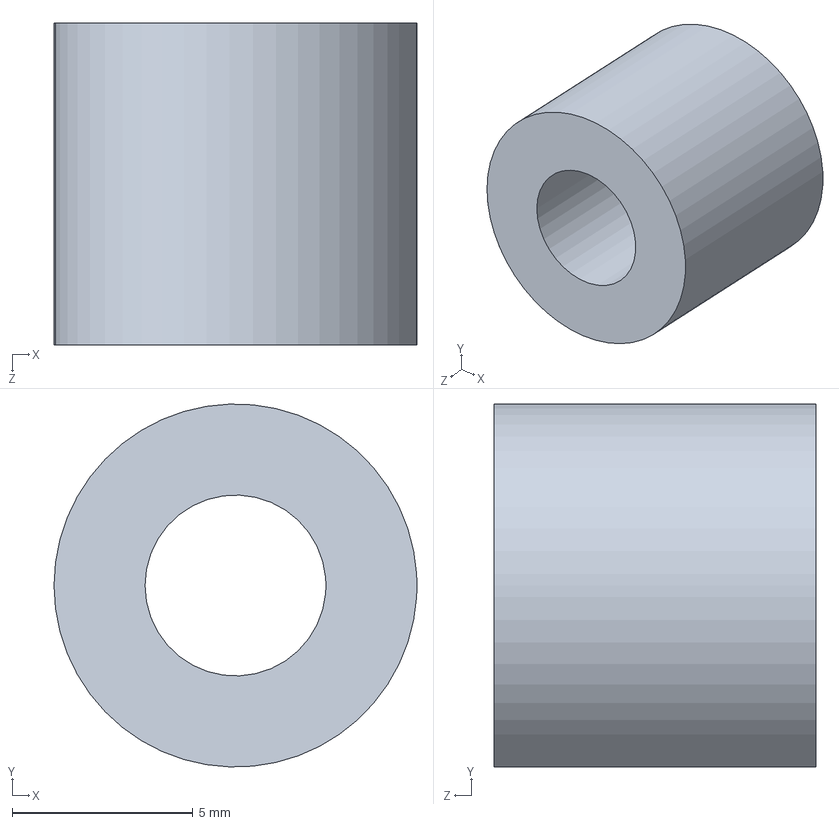
[picture p64: CAD file, 2016-11-26]
Mechanical/CAD/Model-F/Drive Train/ss_mf_v0_Pinion.SLDPRT
10.0 x 10.0 x 8.89 mm
