saunair/Stepping-Stones/Mechanical/CAD/Model-F/PCB/ss_mf_v0_ArduinoMega.SLDPRT

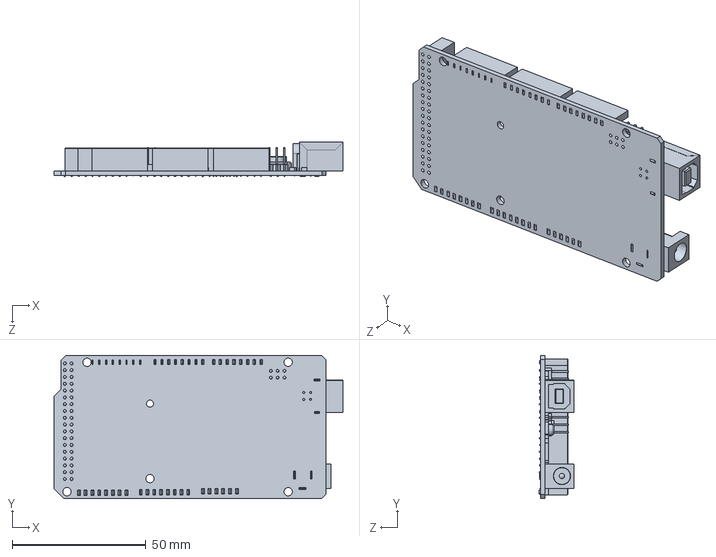
[picture p65: CAD file, 2016-11-26]
Mechanical/CAD/Model-F/PCB/ss_mf_v0_ArduinoMega.SLDPRT
107.9 x 53.4 x 13.0 mm
