saunair/Stepping-Stones/Mechanical/CAD/Model-S/ss_ms_v1_ESC.SLDPRT

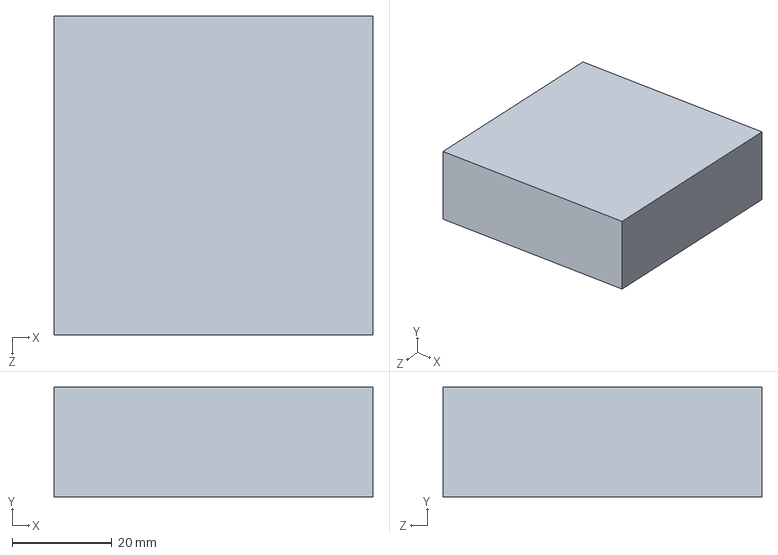
[picture p66: CAD file, 2017-03-11]
Mechanical/CAD/Model-S/ss_ms_v1_ESC.SLDPRT
64.0 x 22.0 x 64.0 mm
