saunair/Stepping-Stones/Mechanical/CAD/Force Calibration Rig/Rear Skate Rig Block.SLDPRT

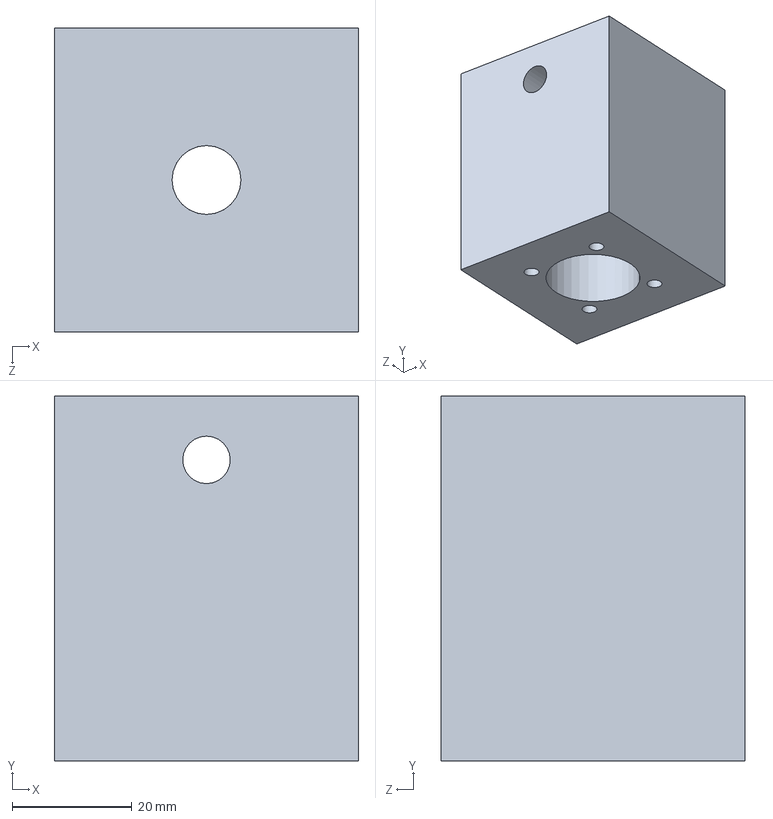
[picture p67: CAD file, 2017-03-11]
Mechanical/CAD/Force Calibration Rig/Rear Skate Rig Block.SLDPRT
50.8 x 61.0 x 50.8 mm
