saunair/Stepping-Stones/Mechanical/CAD/Model-F/SanjaysShoeStandin.SLDPRT

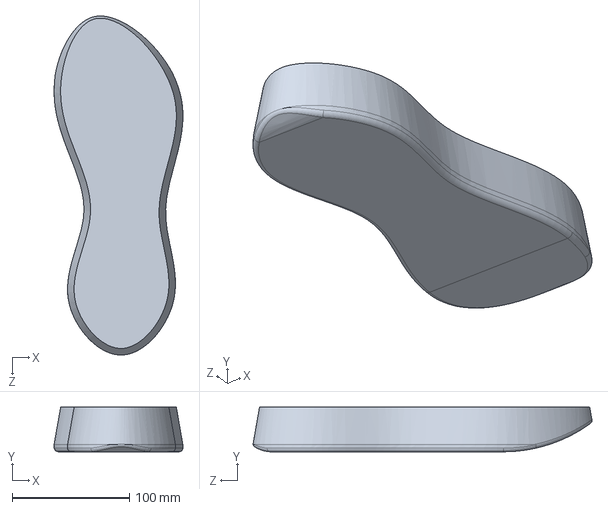
[picture p68: CAD file, 2016-11-26]
Mechanical/CAD/Model-F/SanjaysShoeStandin.SLDPRT
110.1 x 38.1 x 289.6 mm
