saunair/Stepping-Stones/Mechanical/CAD/Model-F/Drive Train/ss_mf_v0_Gearbox.SLDPRT

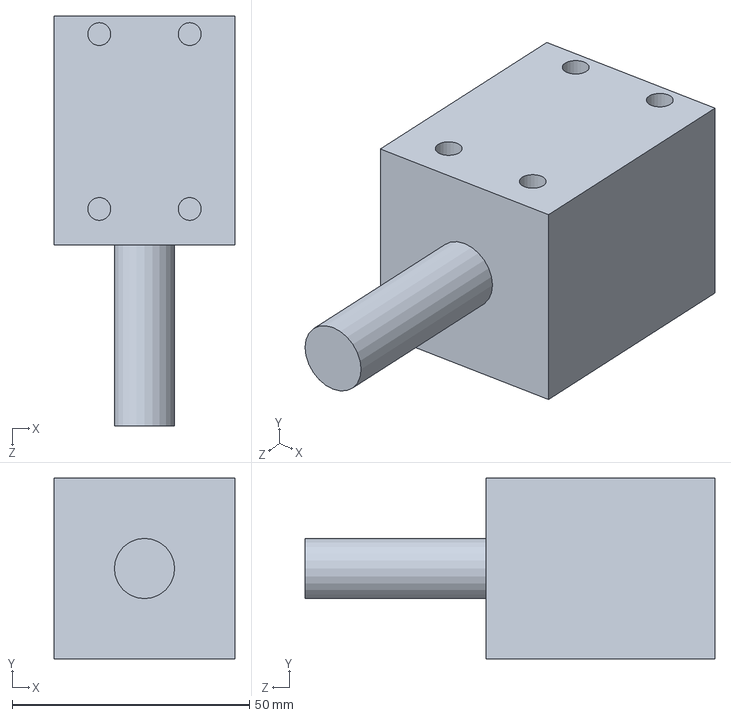
[picture p69: CAD file, 2016-11-26]
Mechanical/CAD/Model-F/Drive Train/ss_mf_v0_Gearbox.SLDPRT
38.1 x 38.1 x 86.4 mm
