saunair/Stepping-Stones/Mechanical/CAD/Model-F/PCB/ss_mf_v1_pcbMountP2.SLDPRT

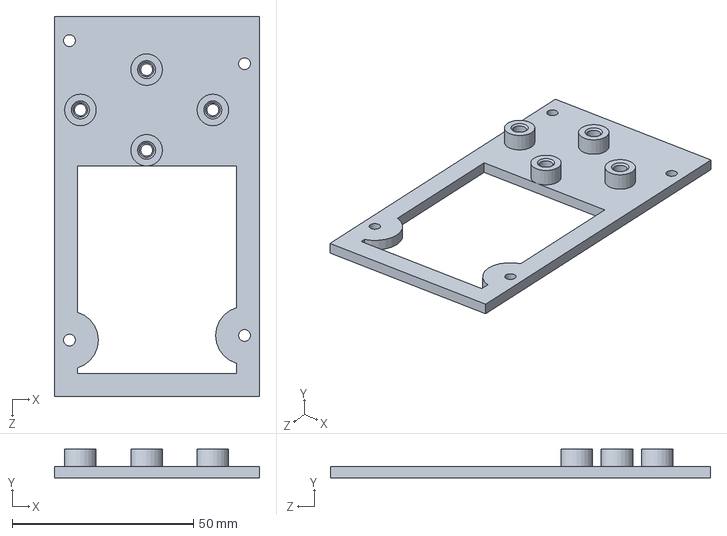
[picture p70: CAD file, 2016-11-26]
Mechanical/CAD/Model-F/PCB/ss_mf_v1_pcbMountP2.SLDPRT
56.5 x 7.94 x 104.8 mm
