saunair/Stepping-Stones/Mechanical/CAD/Model-F/ss_mf_v1_BasePlate.SLDPRT

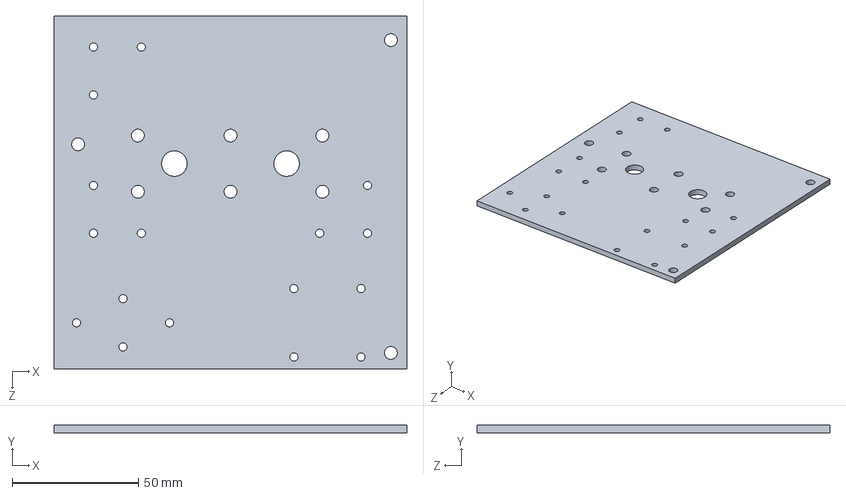
[picture p71: CAD file, 2016-11-26]
Mechanical/CAD/Model-F/ss_mf_v1_BasePlate.SLDPRT
139.7 x 3.17 x 139.7 mm
