saunair/Stepping-Stones/Mechanical/CAD/Model-F/Drive Train/ss_mf_v0_Gearbox2.SLDPRT

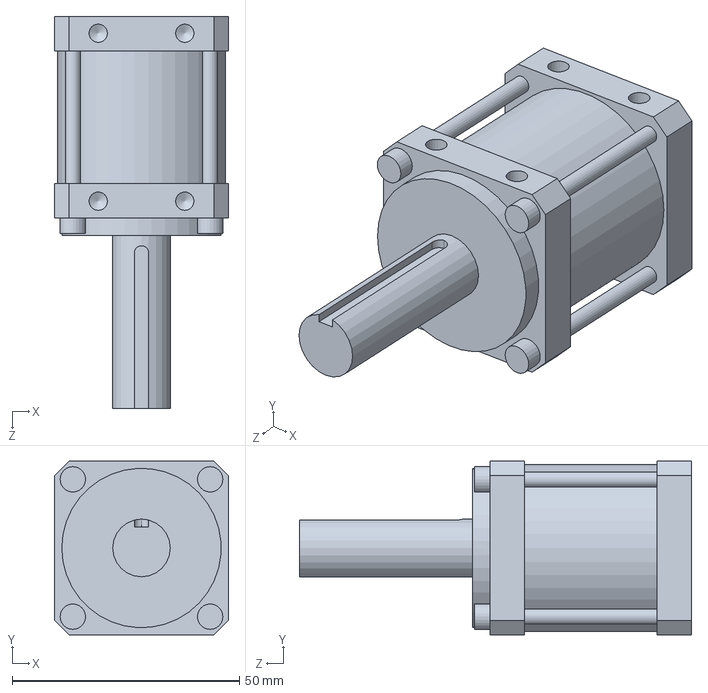
[picture p72: CAD file, 2016-11-26]
Mechanical/CAD/Model-F/Drive Train/ss_mf_v0_Gearbox2.SLDPRT
38.3 x 38.2 x 86.3 mm
