saunair/Stepping-Stones/Mechanical/CAD/Model-F/ss_mf_v1_TopPlateBack.SLDPRT

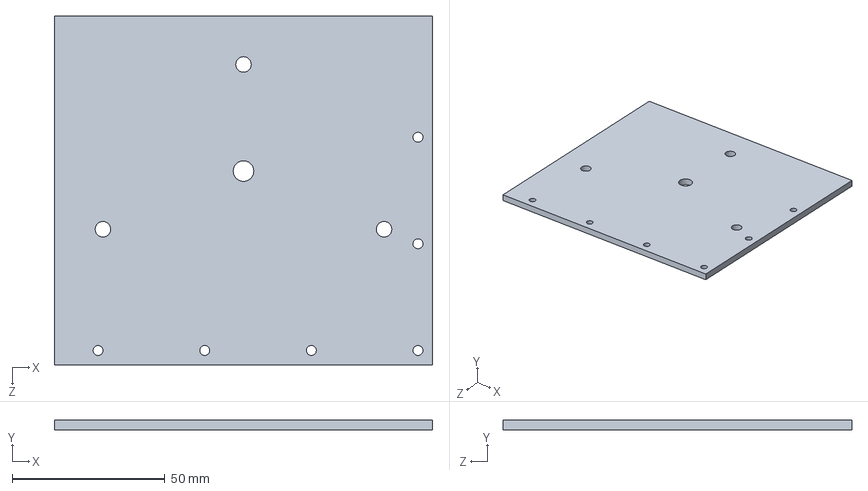
[picture p73: CAD file, 2016-11-26]
Mechanical/CAD/Model-F/ss_mf_v1_TopPlateBack.SLDPRT
123.8 x 3.17 x 114.3 mm
