saunair/Stepping-Stones/Mechanical/CAD/Model-F/Drive Train/ss_mf_v0_Bearing.SLDPRT

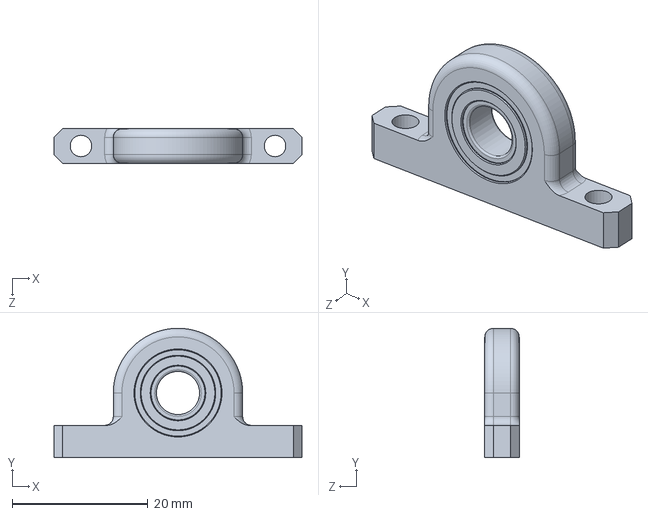
[picture p74: CAD file, 2016-11-26]
Mechanical/CAD/Model-F/Drive Train/ss_mf_v0_Bearing.SLDPRT
36.5 x 19.0 x 5.08 mm
