saunair/Stepping-Stones/Mechanical/CAD/Model-F/KoushiksShoeStandin.SLDPRT

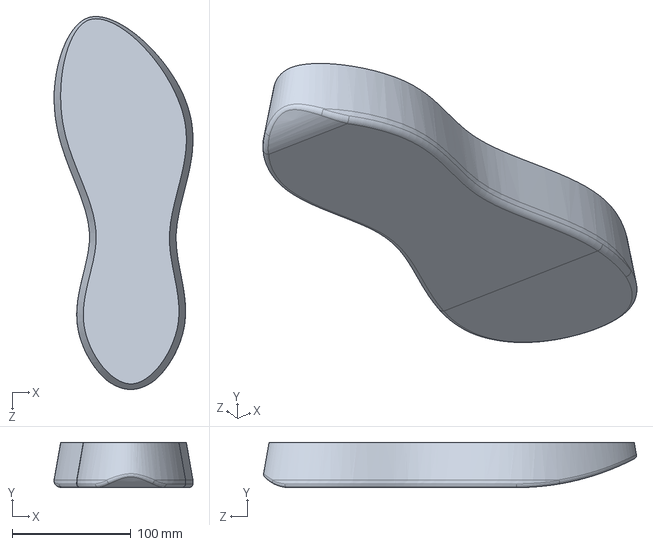
[picture p75: CAD file, 2016-11-26]
Mechanical/CAD/Model-F/KoushiksShoeStandin.SLDPRT
117.2 x 38.1 x 314.5 mm
