saunair/Stepping-Stones/Mechanical/CAD/Model-F/BradsShoeStandin.SLDPRT

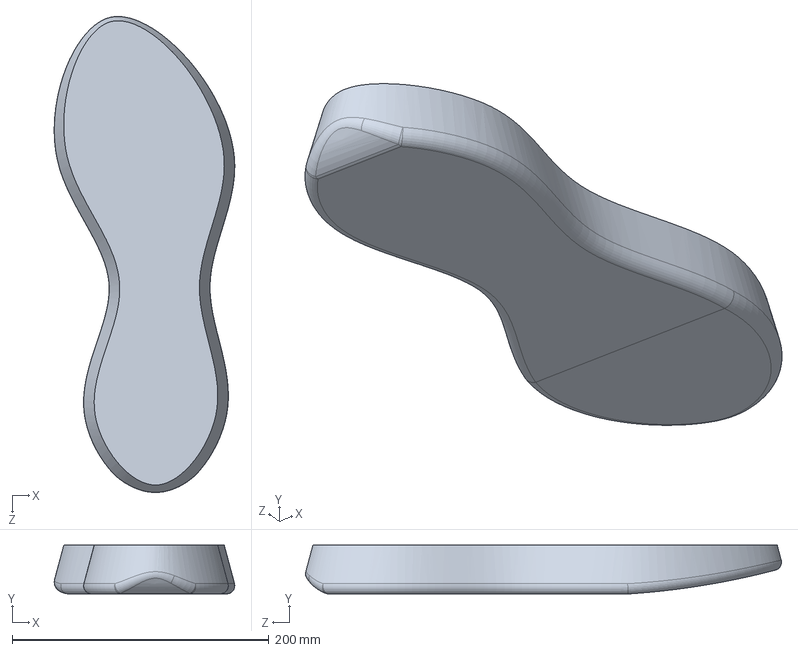
[picture p77: CAD file, 2016-11-26]
Mechanical/CAD/Model-F/BradsShoeStandin.SLDPRT
140.7 x 38.1 x 370.9 mm
