saunair/Stepping-Stones/Mechanical/CAD/Model-F/Drive Train/ss_mf_v0_MotorFront.SLDPRT

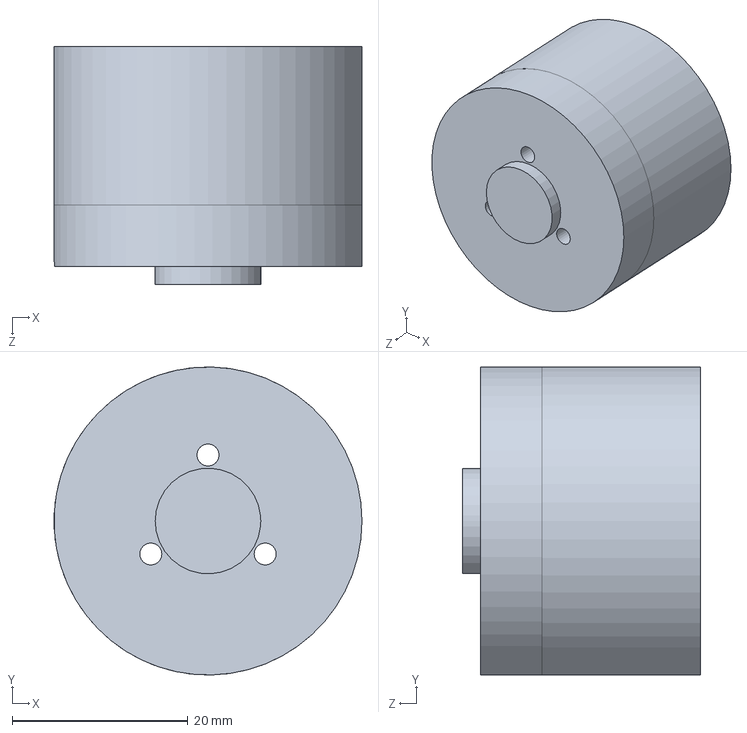
[picture p78: CAD file, 2016-11-26]
Mechanical/CAD/Model-F/Drive Train/ss_mf_v0_MotorFront.SLDPRT
35.0 x 35.0 x 27.0 mm
