saunair/Stepping-Stones/Mechanical/CAD/Model-F/ss_mf_v0_IMU.SLDPRT

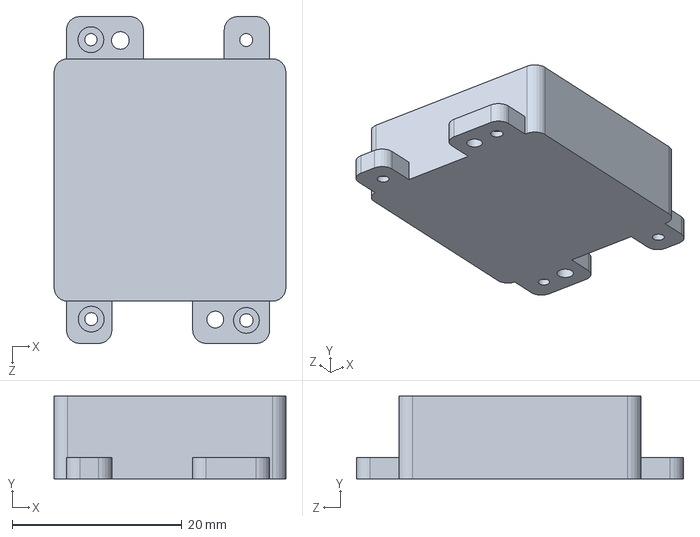
[picture p79: CAD file, 2016-11-26]
Mechanical/CAD/Model-F/ss_mf_v0_IMU.SLDPRT
27.3 x 9.75 x 38.5 mm
