saunair/Stepping-Stones/Mechanical/CAD/Model-F/Drive Train/ss_mf_v0_Encoder.SLDPRT

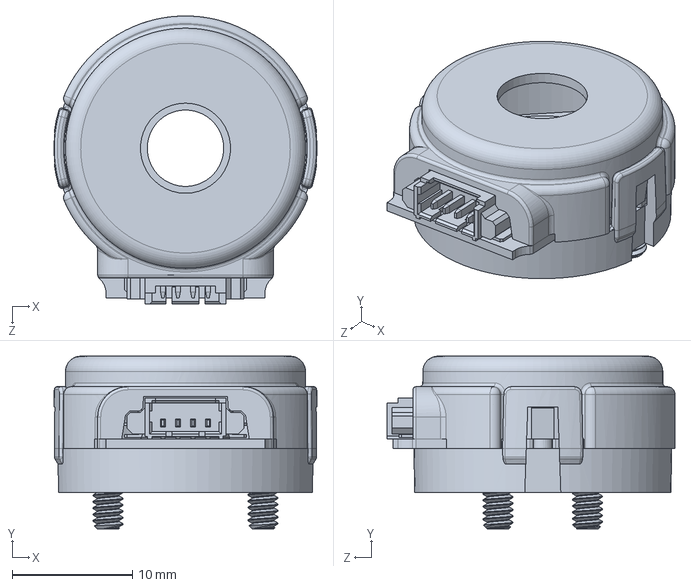
[picture p80: CAD file, 2016-11-26]
Mechanical/CAD/Model-F/Drive Train/ss_mf_v0_Encoder.SLDPRT
21.9 x 14.4 x 23.9 mm
