saunair/Stepping-Stones/Arduino/Skate/buffer.cpp

/*
	Copyright 2012-2014 Benjamin Vedder	benjamin@vedder.se

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
    You should have received a copy of the GNU General Public License
    along with this program.  If not, see <http://www.gnu.org/licenses/>.
    */

/*
 * buffer.c
 *
 *  Created on: 13 maj 2013
 *      Author: benjamin
 */

#include "buffer.h"

void buffer_append_int16(uint8_t* buff, int16_t number, int32_t *index) {
	buff[(*index)++] = number >> 8;
	buff[(*index)++] = number;
}

void buffer_append_uint16(uint8_t* buff, uint16_t number, int32_t *index) {
	buff[(*index)++] = number >> 8;
	buff[(*index)++] = number;
}

void buffer_append_int32(uint8_t* buff, int32_t number, int32_t *index) {
	buff[(*index)++] = number >> 24;
	buff[(*index)++] = number >> 16;
	buff[(*index)++] = number >> 8;
	buff[(*index)++] = number;
}

void buffer_append_uint32(uint8_t* buff, uint32_t number, int32_t *index) {
	buff[(*index)++] = number >> 24;
	buff[(*index)++] = number >> 16;
	buff[(*index)++] = number >> 8;
	buff[(*index)++] = number;
}

void buffer_append_float16(uint8_t* buff, float number, float scale, int32_t *index) {
    buffer_append_int16(buff, (int16_t)(number * scale), index);
}

void buffer_append_float32(uint8_t* buff, float number, float scale, int32_t *index) {
    buffer_append_int32(buff, (int32_t)(number * scale), index);
}

int16_t buffer_get_int16(const uint8_t *buff, int32_t *index) {
	int16_t res =	((uint16_t) buff[*index]) << 8 |
					((uint16_t) buff[*index + 1]);
	*index += 2;
	return res;
}

uint16_t buffer_get_uint16(const uint8_t *buff, int32_t *index) {
	uint16_t res = 	((uint16_t) buff[*index]) << 8 |
					((uint16_t) buff[*index + 1]);
	*index += 2;
	return res;
}

int32_t buffer_get_int32(const uint8_t *buff, int32_t *index) {
	int32_t res =	((uint32_t) buff[*index]) << 24 |
					((uint32_t) buff[*index + 1]) << 16 |
					((uint32_t) buff[*index + 2]) << 8 |
					((uint32_t) buff[*index + 3]);
	*index += 4;
	return res;
}

uint32_t buffer_get_uint32(const uint8_t *buff, int32_t *index) {
	uint32_t res =	((uint32_t) buff[*index]) << 24 |
					((uint32_t) buff[*index + 1]) << 16 |
					((uint32_t) buff[*index + 2]) << 8 |
					((uint32_t) buff[*index + 3]);
	*index += 4;
	return res;
}

float buffer_get_float16(const uint8_t *buff, float scale, int32_t *index) {
    return (float)buffer_get_int16(buff, index) / scale;
}

float buffer_get_float32(const uint8_t *buff, float scale, int32_t *index) {
    return (float)buffer_get_int32(buff, index) / scale;
}
