saunair/Stepping-Stones/Arduino/Skate/UM.h

#ifndef UM_H
#define UM_H

#if defined(ARDUINO) && ARDUINO >= 100
#include "Arduino.h"
#else
#include "WProgram.h"
#endif

#include <stdlib.h>

class UM{
public:
	float gyro_x, gyro_y, gyro_z, accel_x, accel_y, accel_z;
	float quatx, quaty, quatz, quatw;
  int quatA, quatB, quatC, quatD;
  char updates;
	
	UM();
	
	bool encode(byte c);
	
private:

	int state;
	
	enum {STATE_ZERO,STATE_S,STATE_SN,STATE_SNP,STATE_PT,STATE_DATA,STATE_CHK1,STATE_CHK0};
	
	byte packet_type;
	byte address;
	bool packet_is_batch;
	byte batch_length;
	bool packet_has_data;
	byte data[30];
	byte data_length;
	byte data_index;

	byte checksum1;		// First byte of checksum
	byte checksum0;		// Second byte of checksum

	unsigned short checksum10;			// Checksum received from packet
	unsigned short computed_checksum;	// Checksum computed from bytes received
	
	bool checksum(void);
	
	void save(void);
};

#endif
